LouDnl/USBSID-Pico/.github/wiki/Midi/Basics.md

# Midi basics
USBSID-Pico supports (Web)Midi over USB that acts as Midi device that can receive Midi commands.

See the [Midi Manual](https://github.com/LouDnl/USBSID-Pico/blob/master/doc/USBSID-Pico%20midi%20manual.adoc) on how you can use USBSID-Pico with Midi.
