LouDnl/USBSID-Pico/.github/wiki/Midi/Strudel.md

# Index
* [Strudel.cc](#strudelcc)
* [Notes](#notes)
* [Strudel examples](#strudel-examples)

# Strudel.cc
_Excerpt from Strudel website_
[Getting Started](https://strudel.cc/workshop/getting-started/)
With Strudel, you can expressively write dynamic music pieces.
It is an official port of the [Tidal Cycles](https://tidalcycles.org/) pattern language to JavaScript.
You don’t need to know JavaScript or Tidal Cycles to make music with Strudel. This interactive tutorial will guide you through the basics of Strudel.
The best place to actually make music with Strudel is the [Strudel REPL](https://strudel.cc)
## Strudel and USBSID-Pico
With it's WebMidi support you can use USBSID-Pico directly from your browser with [Strudel.cc](https://strudel.cc)

# Strudel Examples
See [.js examples](https://github.com/LouDnl/USBSID-Pico/tree/master/examples/midi/strudel/)
