LouDnl/USBSID-Pico/.github/wiki/Midi/TidalCycles.md

# Index
* [Tidal Cycles](#tidal-cycles)
* [SuperCollider Startup file (example)](#supercollider-startup-file-example)
* [Tidal examples](#tidal-examples)

# Tidal Cycles
_Excerpt from the Tidal Cycles website_
[Tidal Cycles](https://tidalcycles.org/) (or 'Tidal' for short) is a free/open source live coding environment for algorithmic patterns, written in Haskell. Tidal is using SuperCollider, another open-source software, for synthesis and I/O.
## Tidal Cycles and USBSID-Pico
With it's Midi over USB support you can use USBSID-Pico with [Tidal Cycles](https://tidalcycles.org/).  
This however does require you to follow the installation guide on the [documentation pages](https://tidalcycles.org/docs/).
* [Linux](https://tidalcycles.org/docs/getting-started/linux_install/)
* [MacOS](https://tidalcycles.org/docs/getting-started/macos_install/)
* [Windows](https://tidalcycles.org/docs/getting-started/windows_install/)

# SuperCollider Startup file (example)
See [startup.scd](https://github.com/LouDnl/USBSID-Pico/tree/master/examples/midi/superdirt-tidalcycles/startup.scd)

# Tidal examples
Below are my personal notes and scribbles, if they don't work then they don't work.
See [.tidal examples](https://github.com/LouDnl/USBSID-Pico/tree/master/examples/midi/superdirt-tidalcycles/)
