LouDnl/USBSID-Pico/doc/USBSID-Volume-daughterboard.pdf

# USBSID-Volume daughterboard

### Author: LouD - generated on 2026-07-08

# Table of Contents

# Disclaimer

I do this stuff in my free time for my enjoyment. Since I like to share my joy in creating this with everyone I try my best to provide a working PCB and Firmware. I am in no way an electronics engineer and can give no guarantees that this stuff does not break or damage your hardware, computer, phone, or whatever you try to hook it up to. Be sure to take great care when inserting any real MOS SID chips into the board. While everything has been tested with real chips, this is in no way a guarantee that nothing could go wrong. Use of this board and firmware at your own risk! I am in no way responsible for your damaged hardware. That being said, have fun!

# About

The volume daughterboard is intended as optional addon for USBSID-Pico.
With This board seated you can independently control the volume of the left and right audio channels.
The board is Plug and play compatible with v1.5+ boards.
Compatibility with v1.3 boards is possible with a small modification to provide voltage.

# Usage v1.5

Below is an example of the board seated.
Follow the instructions under Solder jumpers to configure the board for your pcb.


# Usage v1.3

Take great care when using the board with versions v1.3.
Below is an example of the board seated and as you can see the right most pins are unconnected. Follow the instructions under Solder jumpers and Voltage tap to configure the board for your pcb.


# Usage v1.0

Same as with v1.3, please take great care when using the board.
The v1.0 pcb only has 2 pins where the outer pin on each side is Ground. This requires you to make another mod to the board to provide ground to the board. Do this at your own risk, the board is not tested with v1.0 pcb’s.

# Solder jumpers

The board has 4 solder jumpers on the bottom that set the pin functions of 2 two outer most pins for each pinsocket.
These jumpers are marked with V-I-G or G-I-V, G for Ground, I for Input and V for Vdd.

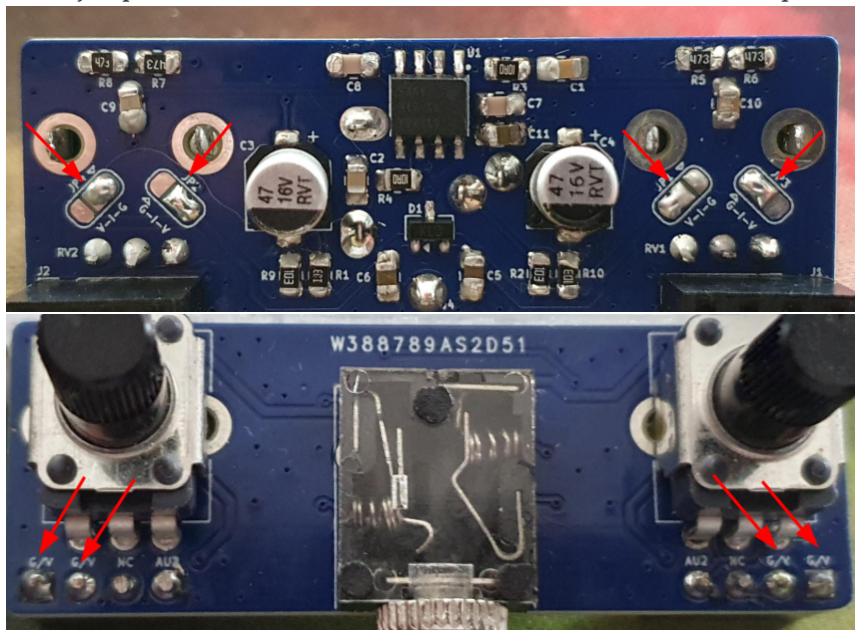
[picture p37: figure]

For v1.5 boards you can solder the jumpers exactly as the picture above, from left to right: V-I-G, G-I-V, V-I-G, G-I-V meaning Input+Ground, Input+VDD, VDD+Input, Ground+Input For v1.3 boards you can solder the jumpers as described below, from left to right:

V-I-G, G-I-V, V-I-G, G-I-V meaning VDD+Input, Ground+Input, Input+Ground, Input+VDD

The socket pins must match the order of the markings on the bottom of the USBSID-Pico PCB. v1.5:

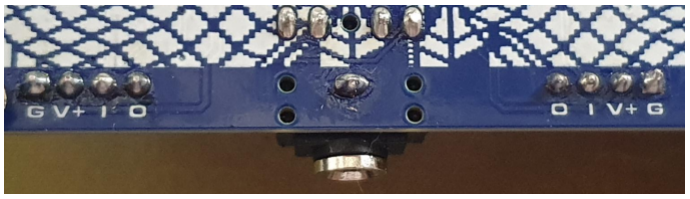
[picture p38: figure]

v1.3:

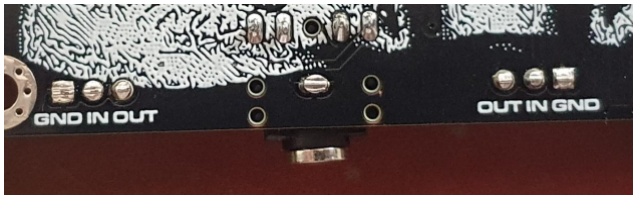
[picture p39: figure]

As you can see the v1.3 boards do not have a voltage pin, this requires you to make a voltage tap wire to any of the fixed points described under Voltage tap.

# Voltage tap

v1.3 pcbs have multiple points to where you can solder a wire to provide voltage to the volume board.
These tap points are described below the picture.

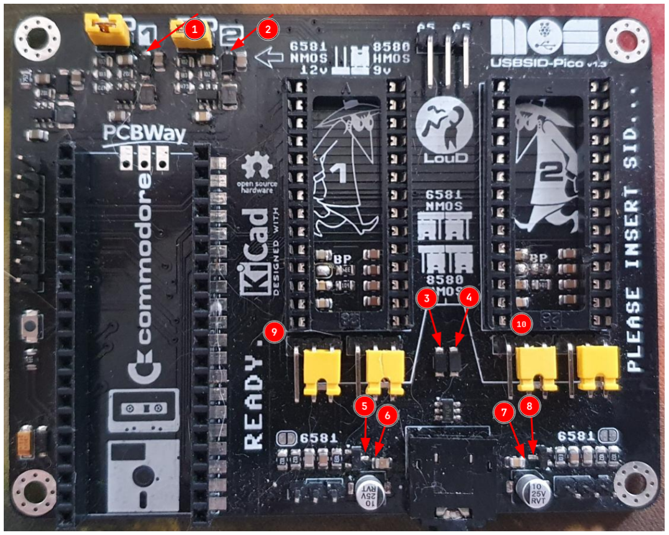
[picture p40: figure]

1. Diode output of SID1 voltage regulator 2. Diode output of SID2 voltage regulator 3. SID1 diode input voltage to audio switch 4. SID2 diode input voltage to audio switch 5. Voltage input to SID1 voltage follower 6. Voltage filter capacitor of SID1 voltage follower 7. Voltage input to SID2 voltage follower 8. Voltage filter capacitor of SID2 voltage follower 9. SID1 VDD in on the bottom of the PCB 10. SID2 VDD in on the bottom of the PCB

# License

# Software License ~ GNUv2

All code written by me in this repository is licensed under the terms of the GNU General Public License as published by the Free Software Foundation, version 2. Any code in this repository that is not written by me automatically falls under the licensing conditions by the authors of said code as mentioned in the source code header. For for more information about this license please read the LICENSE document in the root of the USBSID-Pico repository.

# Configtool Software License ~ EPLv2

# USBSID-Pico v1.5 PCB Hardware License ~ CC BY-NC-

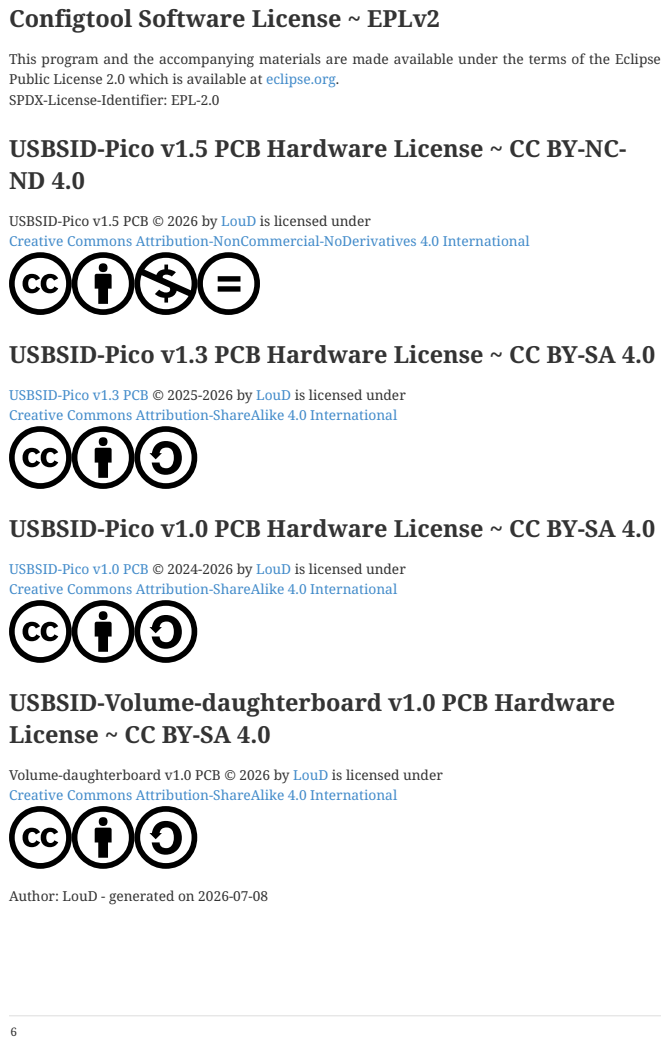
[picture p41: page 6]

This program and the accompanying materials are made available under the terms of the Eclipse
Public License 2.0 which is available at eclipse.org.
SPDX-License-Identifier: EPL-2.0

USBSID-Pico v1.5 PCB © 2026 by LouD (https://github.com/LouDnl) is licensed under
Creative Commons Attribution-NonCommercial-NoDerivatives 4.0 International (https://creativecommons.org/licenses/by-nc-nd/4.0/)

USBSID-Pico v1.3 PCB Hardware License ~ CC BY-SA 4.0

USBSID-Pico v1.3 PCB (https://github.com/LouDnl/USBSID-Pico/tree/master/hardware/USBSID-Pico-v1.3) © 2025-2026 by LouD (https://github.com/LouDnl) is licensed under
Creative Commons Attribution-ShareAlike 4.0 International (https://creativecommons.org/licenses/by-sa/4.0/)

USBSID-Pico v1.0 PCB Hardware License ~ CC BY-SA 4.0

USBSID-Pico v1.0 PCB (https://github.com/LouDnl/USBSID-Pico/tree/master/hardware/USBSID-Pico-v1.0) © 2024-2026 by LouD (https://github.com/LouDnl) is licensed under

USBSID-Volume-daughterboard v1.0 PCB Hardware
License ~ CC BY-SA 4.0

Volume-daughterboard v1.0 PCB © 2026 by LouD (https://github.com/LouDnl) is licensed under

Author: LouD - generated on 2026-07-08
