LouDnl/USBSID-Pico/SHOWCASE.md

# Showcase
Videos and/or audio links are subject to be changed or updated at any time.<br>
Visit my [Youtube channel](https://www.youtube.com/channel/UCOu1hPBTsEbG7ZFnk9-29KQ), [other socials](https://github.com/LouDnl) for more examples of the board in action.

### Audio recordings
- [Reed's Flamethrower](media/Reed-Flamethrower.mp3)
- [Fanta - Coma Light 13 (partial recording)](media/Fanta-ComaLight13(partial).mp3)
- [Fanta in Space (partial recording)](media/Fanta-InSpace(partial).mp3)
- [Jammer - Make Some Noise (partial recording)](media/Jammer-MakeSomeNoise(partial).mp3)
- [Mahoney - Musik Run Stop (partial recording)](media/Mahoney-MusikRunStop(partial).mp3)

### MOS8580 chip
| **Van Halen's Jump<br>in Stereo!** | **Flamethrower** | **Coma Light 13** |
|:-:|:-:|:-:|
| Dual MOS8580 (https://www.youtube.com/watch?v=lzvkWlDq2TM)<br><small><sub>by Nordischsound</sub></small> | MOS8580 (https://www.youtube.com/watch?v=Mfbj21ntQXA)<br><small><sub>by Reed</sub></small> | MOS8580 (https://www.youtube.com/watch?v=iXviof4ZtIg)<br><small><sub>by Oxyron</sub></small> |

| **Layers<br>Finnish Gold** | **Mojo<br>Bonzai & Pretzel Logic** | **Spy vs Spy II<br>The Island Caper** |
|:-:|:-:|:-:|
| MOS8580 (https://www.youtube.com/watch?v=UQVDTNV3mgs) | MOS8580 (https://www.youtube.com/watch?v=lXxlArB3VS4) | MOS8580 (https://www.youtube.com/watch?v=B4iYnZELbSc) |

| **Codeboys & Endians** | **No Limit** | **Multiverse 100%<br>with mirrored SID's!** |
|:-:|:-:|:-:|
| MOS8580 (https://www.youtube.com/watch?v=sSDsOih1Wbw)<br><small><sub>by Booze Design</sub></small> | MOS8580 (https://www.youtube.com/watch?v=hJit04tWUaM)<br><small><sub>Quantum tracker demo</sub></small> | Dual MOS8580 (https://www.youtube.com/watch?v=Rr-oq5jBeDg)<br><small><sub>by Nah-Kolor</sub></small> |

###  MOS6581 chip
| **“Raster Bar” (8-bit)** |
|:-:|
| MOS6581 (https://www.youtube.com/watch?v=nh0SxO1y6I0)<br><small><sub>by LukHash</sub></small> |

| **Spy vs Spy** | **Commando** | **Monty on the Run** |
|:-:|:-:|:-:|
| Dual MOS6581 (https://www.youtube.com/watch?v=Me79wiWPoXc) | Dual MOS6581 (https://www.youtube.com/watch?v=5YYzJu9KSuY) | Single MOS6581 (https://www.youtube.com/watch?v=PAHPY8jR4rA) <br><small><sub>by Rob Hubbard</sub></small> |

### Dual SIDKick-Pico with MOS8580 emulation
| **Still Rising**<br><small><sub>Single MOS8580</sub></small> | **The Ghost**<br><small><sub>Single MOS8580</sub></small> |
|:----:|:----:|
| Dual SIDKick-Pico (https://www.youtube.com/watch?v=svsxwElcWS8) <br>by Artline Designs,<br>Bloodsuckers,<br>Extend & Orange | Dual SIDKick-Pico (https://www.youtube.com/watch?v=joGVIwMuugU) <br>by FairLight<br>& Genesis Project |
| **Quad Core demo**<br><small><sub>Quad MOS8580</sub></small> | **Game of Thrones**<br><small><sub>Dual MOS8580</sub></small> |
| Dual SIDKick-Pico as 4x MOS8580 SID (https://www.youtube.com/watch?v=zWvMhORM-sg) <br>by Singular | Dual SIDKick-Pico (https://www.youtube.com/watch?v=lShZ3DHaJg8) <br>by Genesis Project |
