LouDnl/USBSID-Pico/cases/v1.3/spotUP-revisited/README.md

# Cartridge Case by spotUp revisited
- Updated to be v1.3 PCB compatible
- Optional reset button in top lid
  Printable reset pin included
- Optional open top lid
- Optional opening for RGB LED fun in top lid
- Optional openings for jumpers on the bottom in bottom lid
- Design is opensource  
  Change the case to your liking on [Tinkercad](https://www.tinkercad.com/things/9WenaLv3th5-usbsid-pico-v13-case)

# Examples
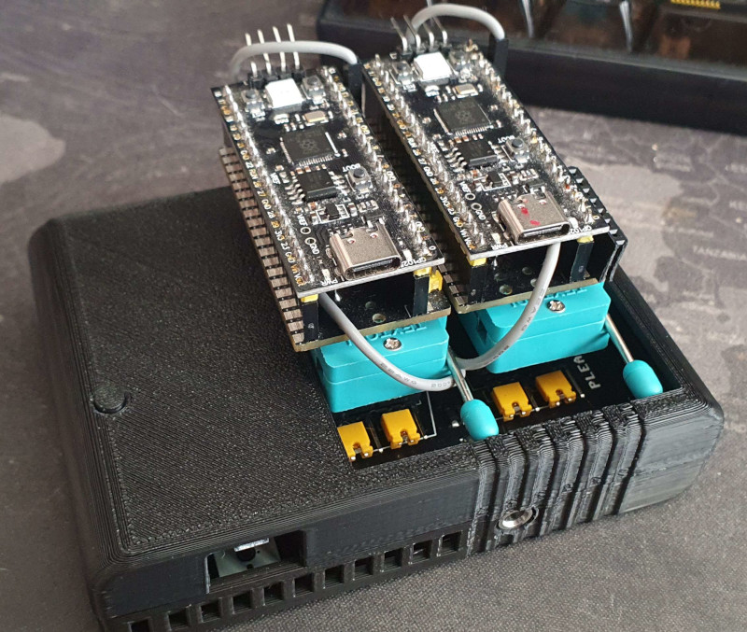
[picture p49: cases/v1.3/spotUP-revisited/v1.3-cartridgecase-top-open.jpg]
Cartridge Case Open Top
  

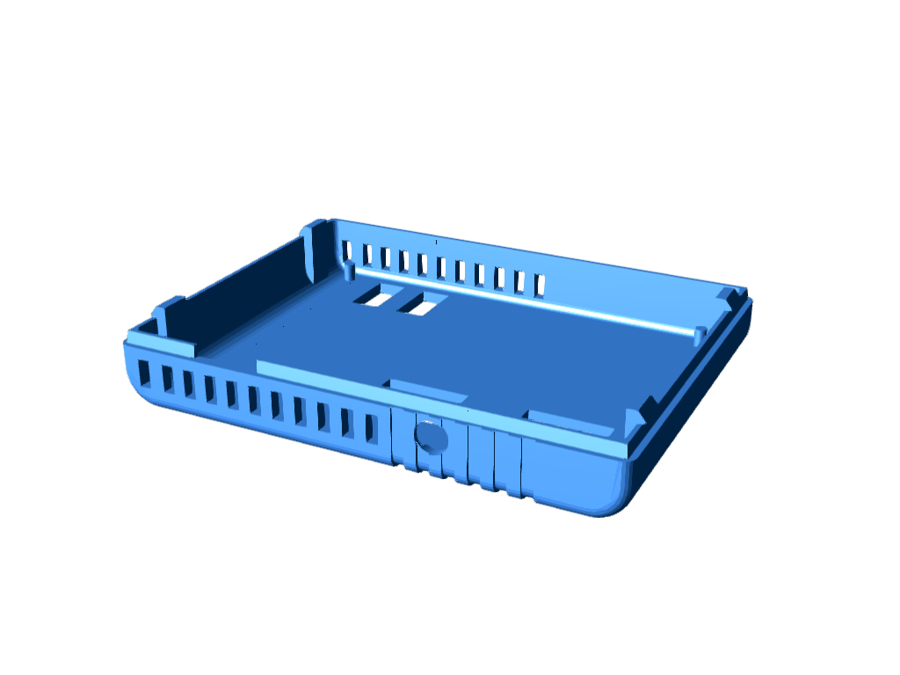
[picture p50: cases/v1.3/spotUP-revisited/USBSID-Pico v1.3 bottom case jumper openings.png]
bottom case

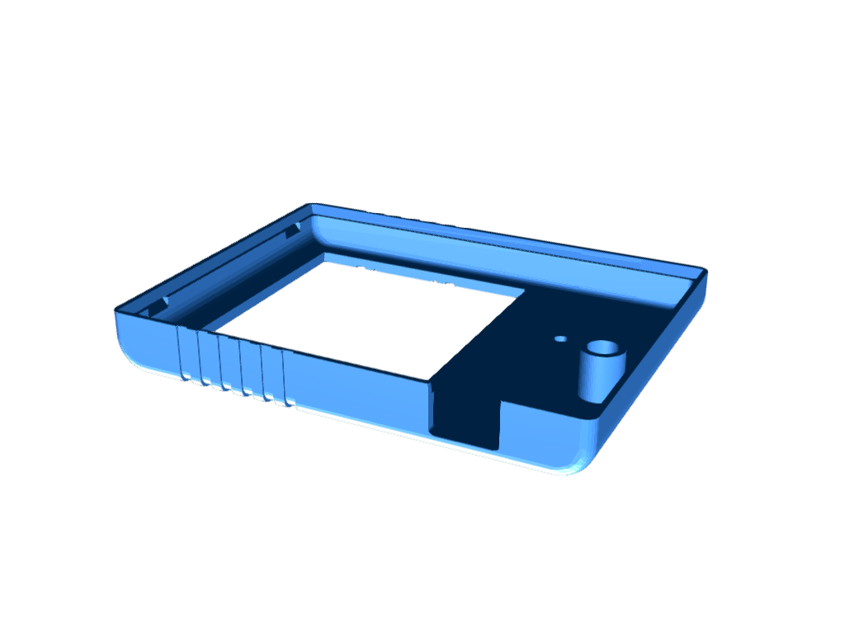
[picture p51: cases/v1.3/spotUP-revisited/USBSID-Pico v1.3 top case open with reset and rgb led opening.png]
top case


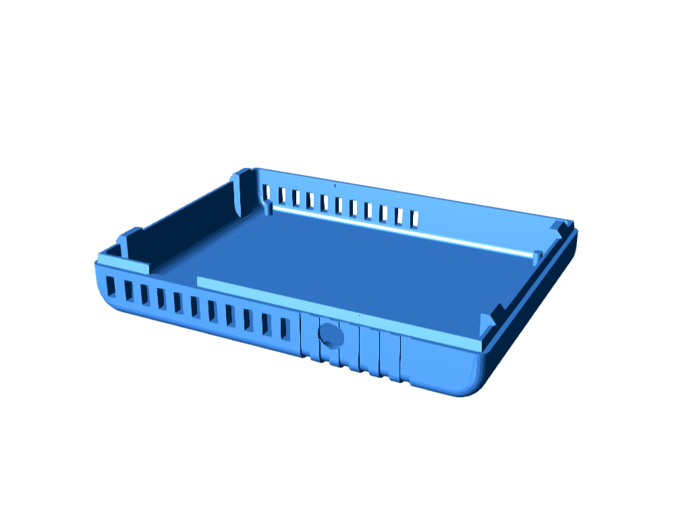
[picture p52: cases/v1.3/spotUP-revisited/USBSID-Pico v1.3 bottom case notched.png]
bottom case

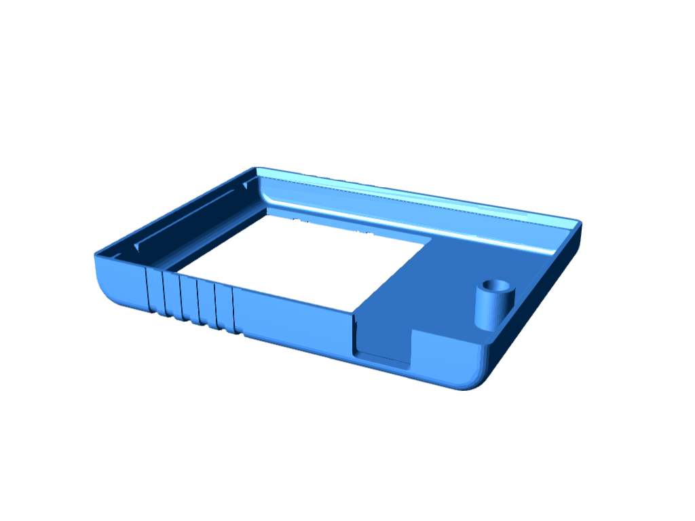
[picture p53: cases/v1.3/spotUP-revisited/USBSID-Pico v1.3 top case open with reset.png]
top case


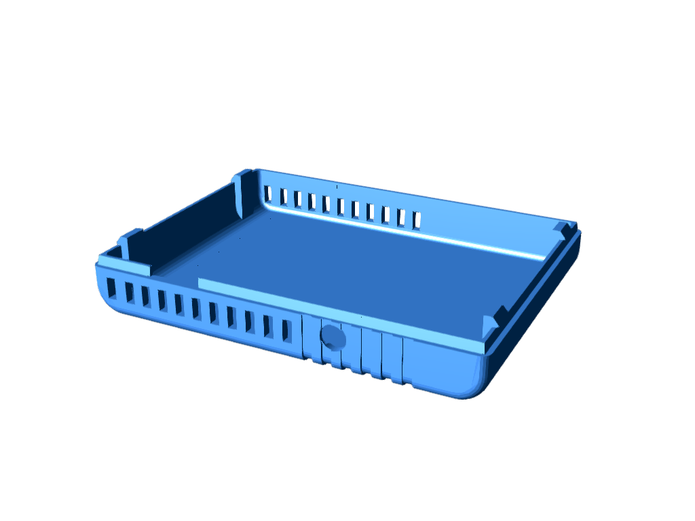
[picture p54: cases/v1.3/spotUP-revisited/USBSID-Pico v1.3 bottom case.png]
bottom case

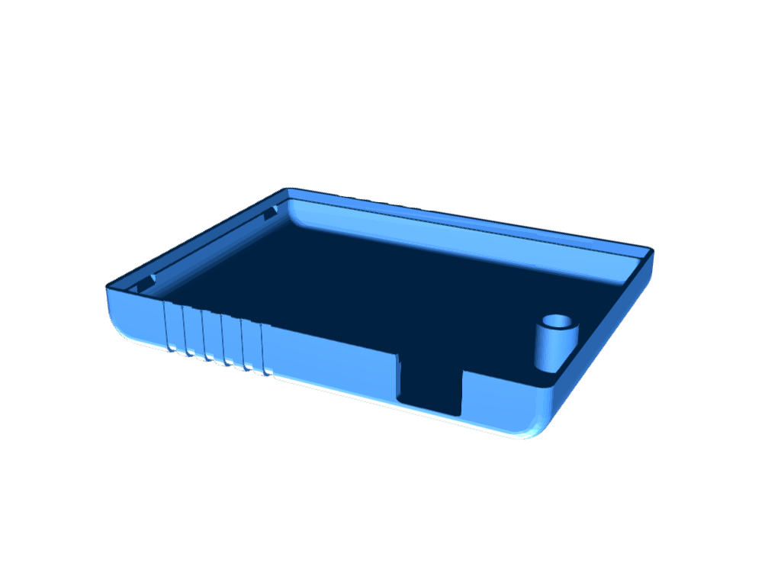
[picture p55: cases/v1.3/spotUP-revisited/USBSID-Pico v1.3 top case with reset.png]
top case
