LouDnl/USBSID-Pico/cases/v1.0/schorsch3000/Readme.md

# 3D-Printed 'boxy' case for the USBSID-pico

# Printing

For printing all you need are the two `.stl` files.

Just print the top and bottom part without support laying on the flat side.

If you want to print a multicolor logo, of a logo cutout, just split the case in parts in your slicer and color or remove the logo.

# Assembly
You'll need 4 M3 screws, 10-15mm in length.

You can tap the holes or just force the screw in.

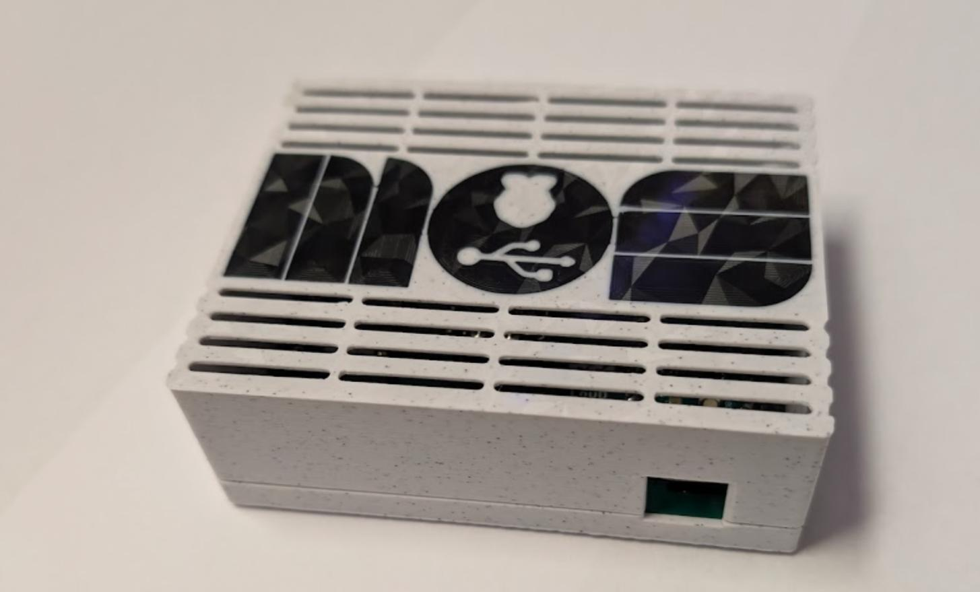
[picture p56: cases/v1.0/schorsch3000/top1.jpg]
top usb side


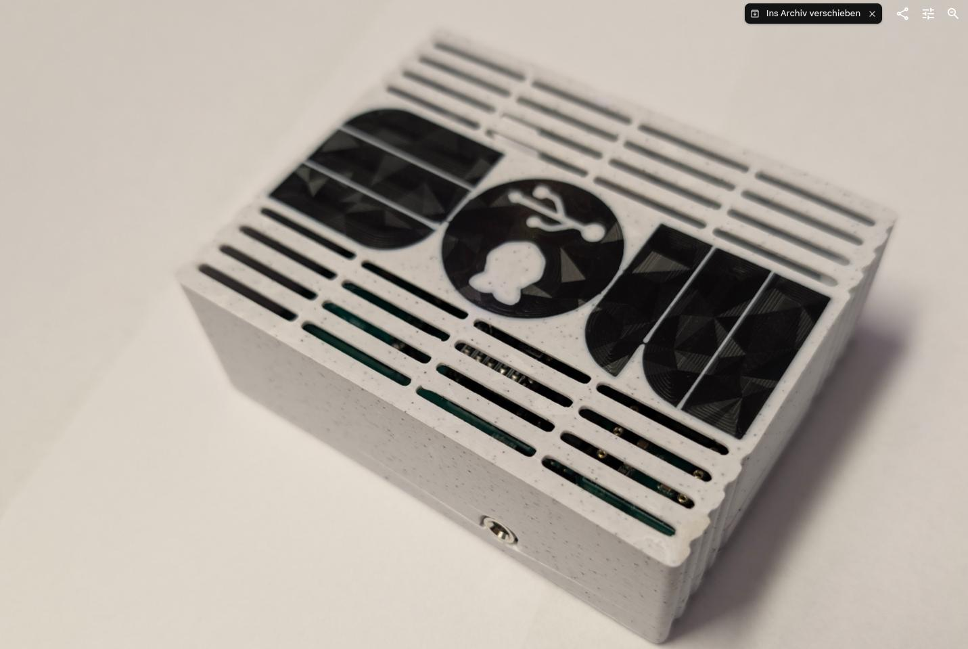
[picture p57: cases/v1.0/schorsch3000/top2.jpg]
top audio side

The Bulge at the Audioport is fixed by now.

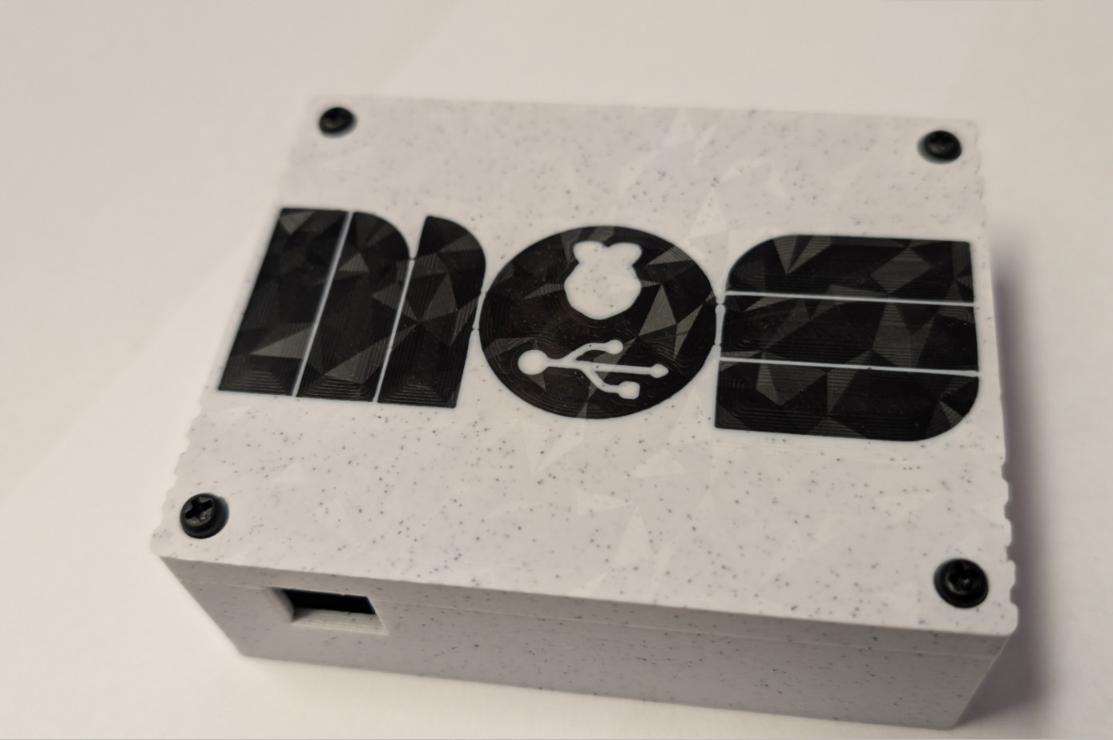
[picture p58: cases/v1.0/schorsch3000/bottom1.jpg]
bottom
