LouDnl/USBSID-Pico/doc/images/v1.5/usbsid-pico-v1.5b-6582-6581-original_1.jpg

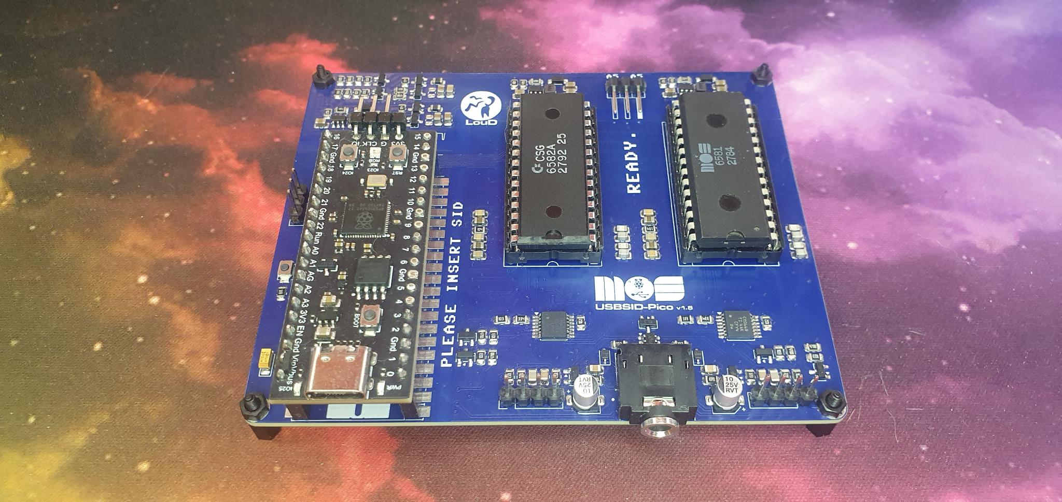
doc/images/v1.5/usbsid-pico-v1.5b-6582-6581-original_1.jpg
