LouDnl/USBSID-Pico/doc/images/v1.5/usbsid-pico-v1.5b-6582-6581-original_2.jpg

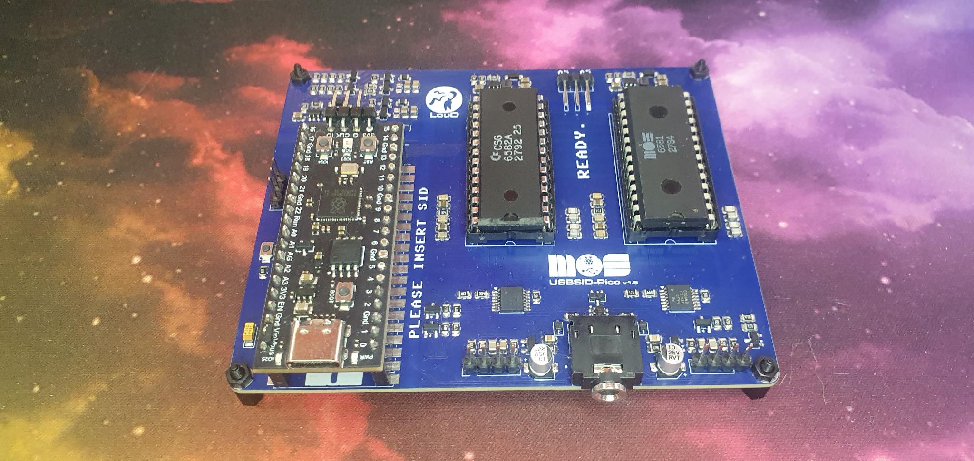
doc/images/v1.5/usbsid-pico-v1.5b-6582-6581-original_2.jpg
