LouDnl/USBSID-Pico/images/pcbv0.2.png

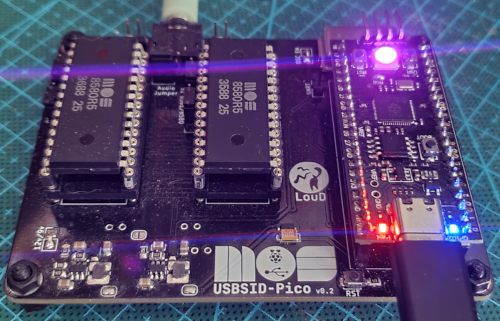
images/pcbv0.2.png
