LouDnl/USBSID-Pico/images/pcbv1.0.jpg

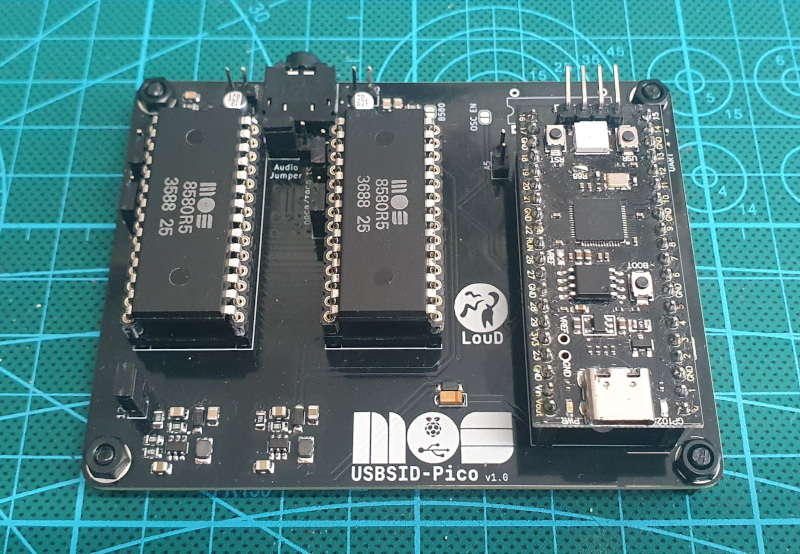
images/pcbv1.0.jpg
