LouDnl/USBSID-Pico/images/pcbv1.3-neon.png

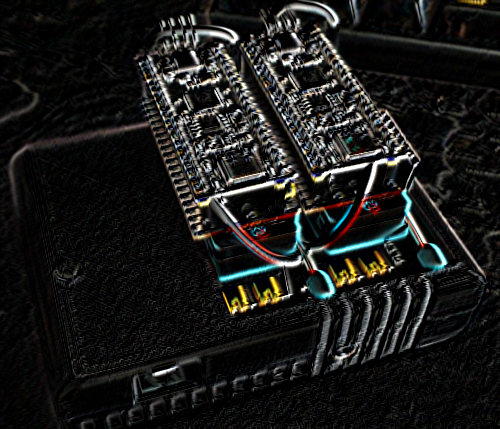
images/pcbv1.3-neon.png
