LouDnl/USBSID-Pico/images/pcbv1.3-pdsid.png

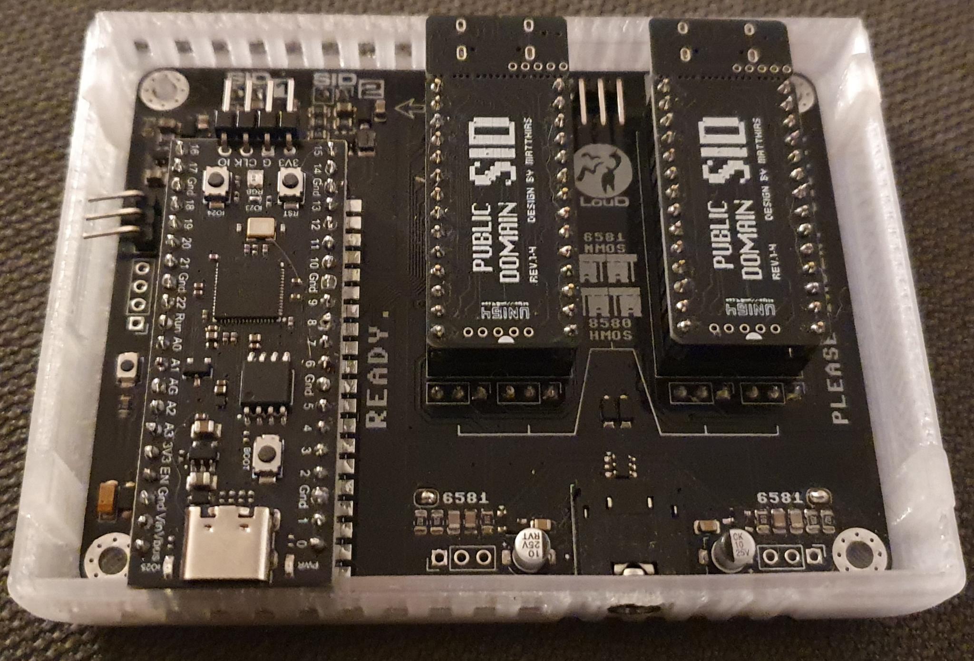
images/pcbv1.3-pdsid.png
