LouDnl/USBSID-Pico/images/pcbway.png

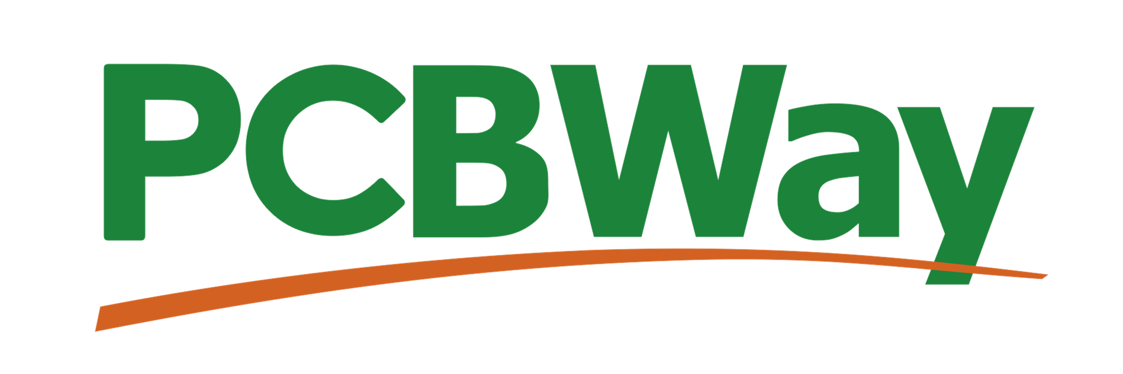
images/pcbway.png
