LouDnl/USBSID-Pico/hardware/v1.0-schematic.pdf

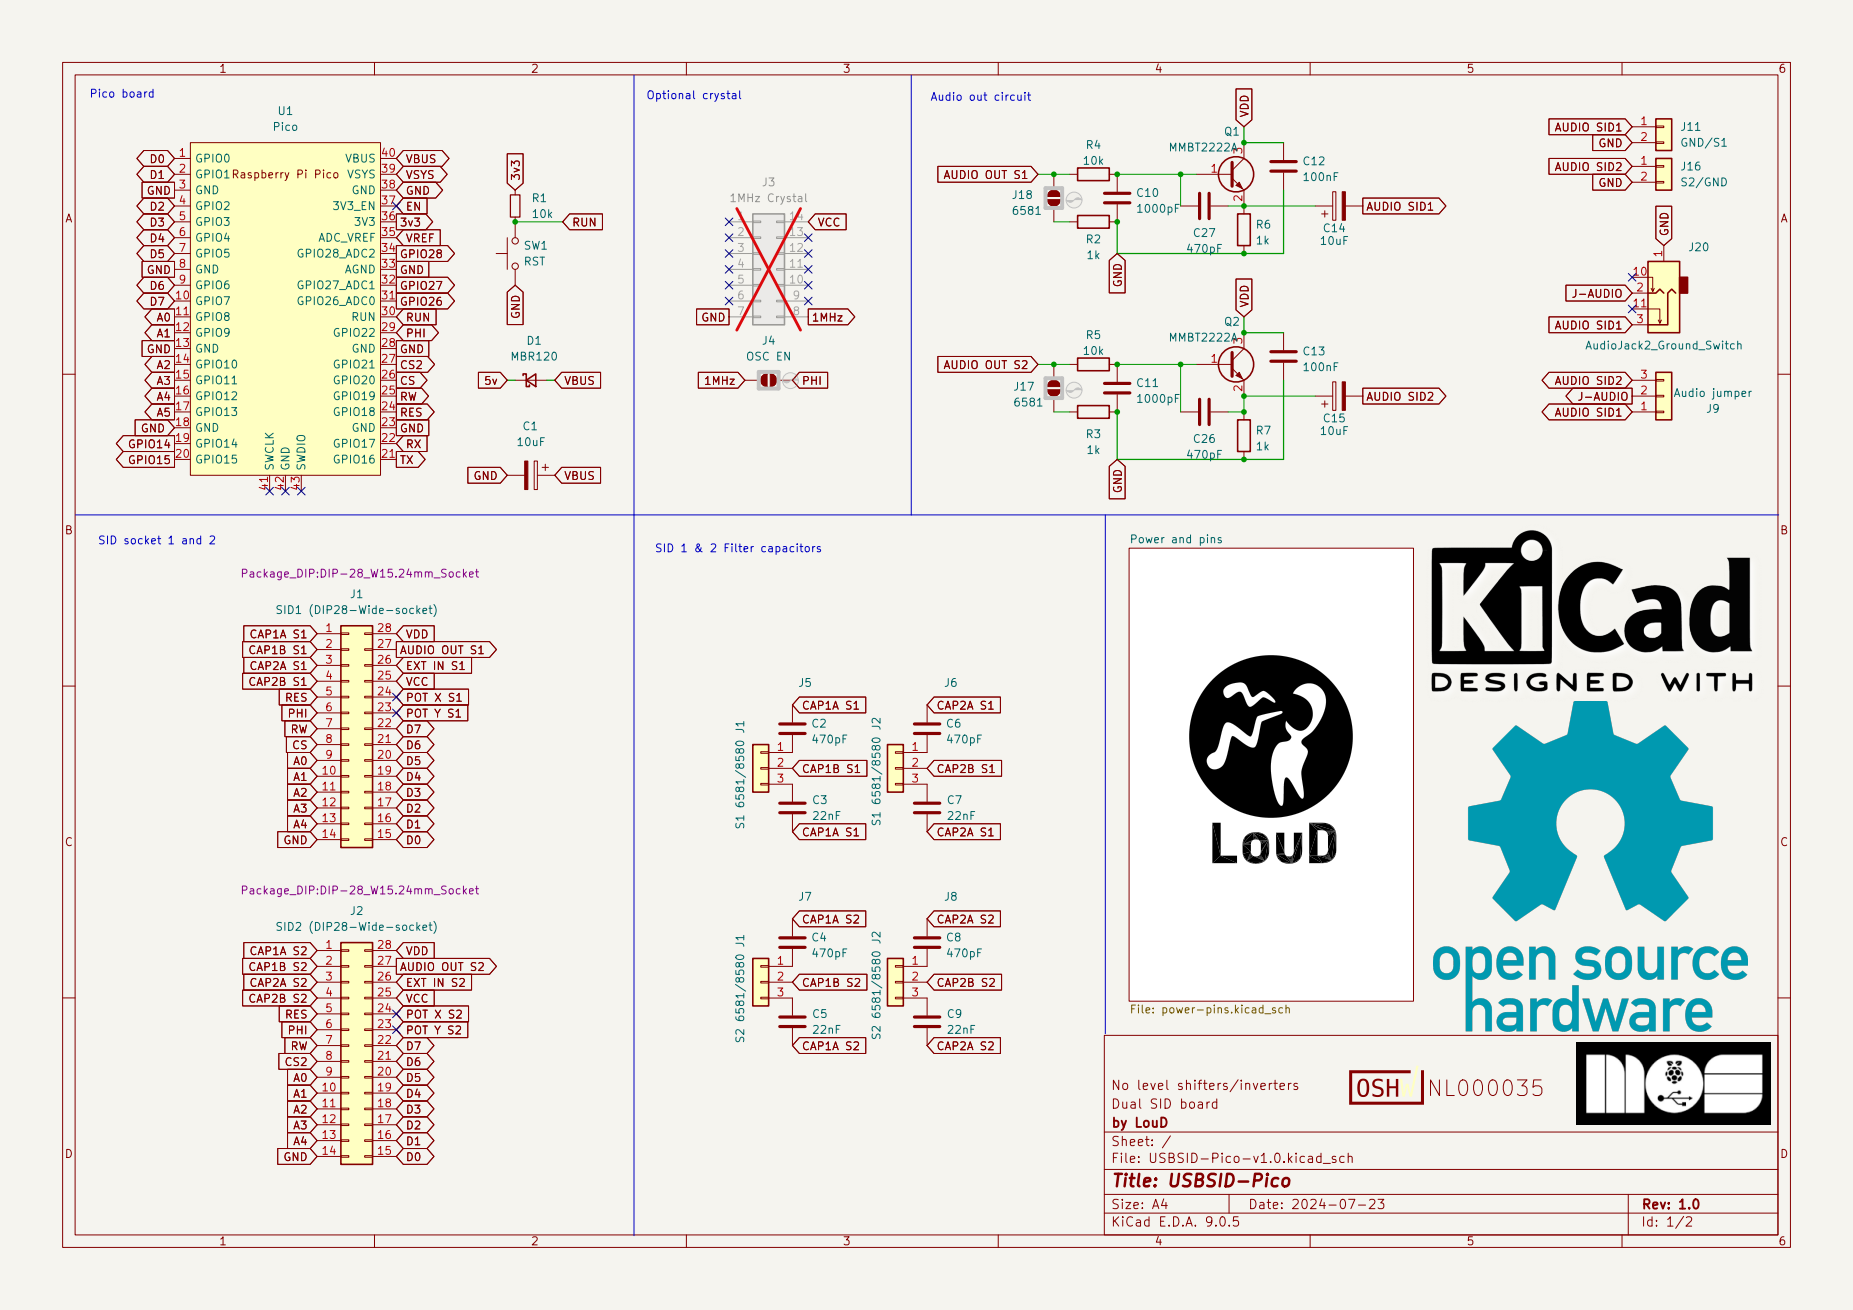
[picture p180: page 1]

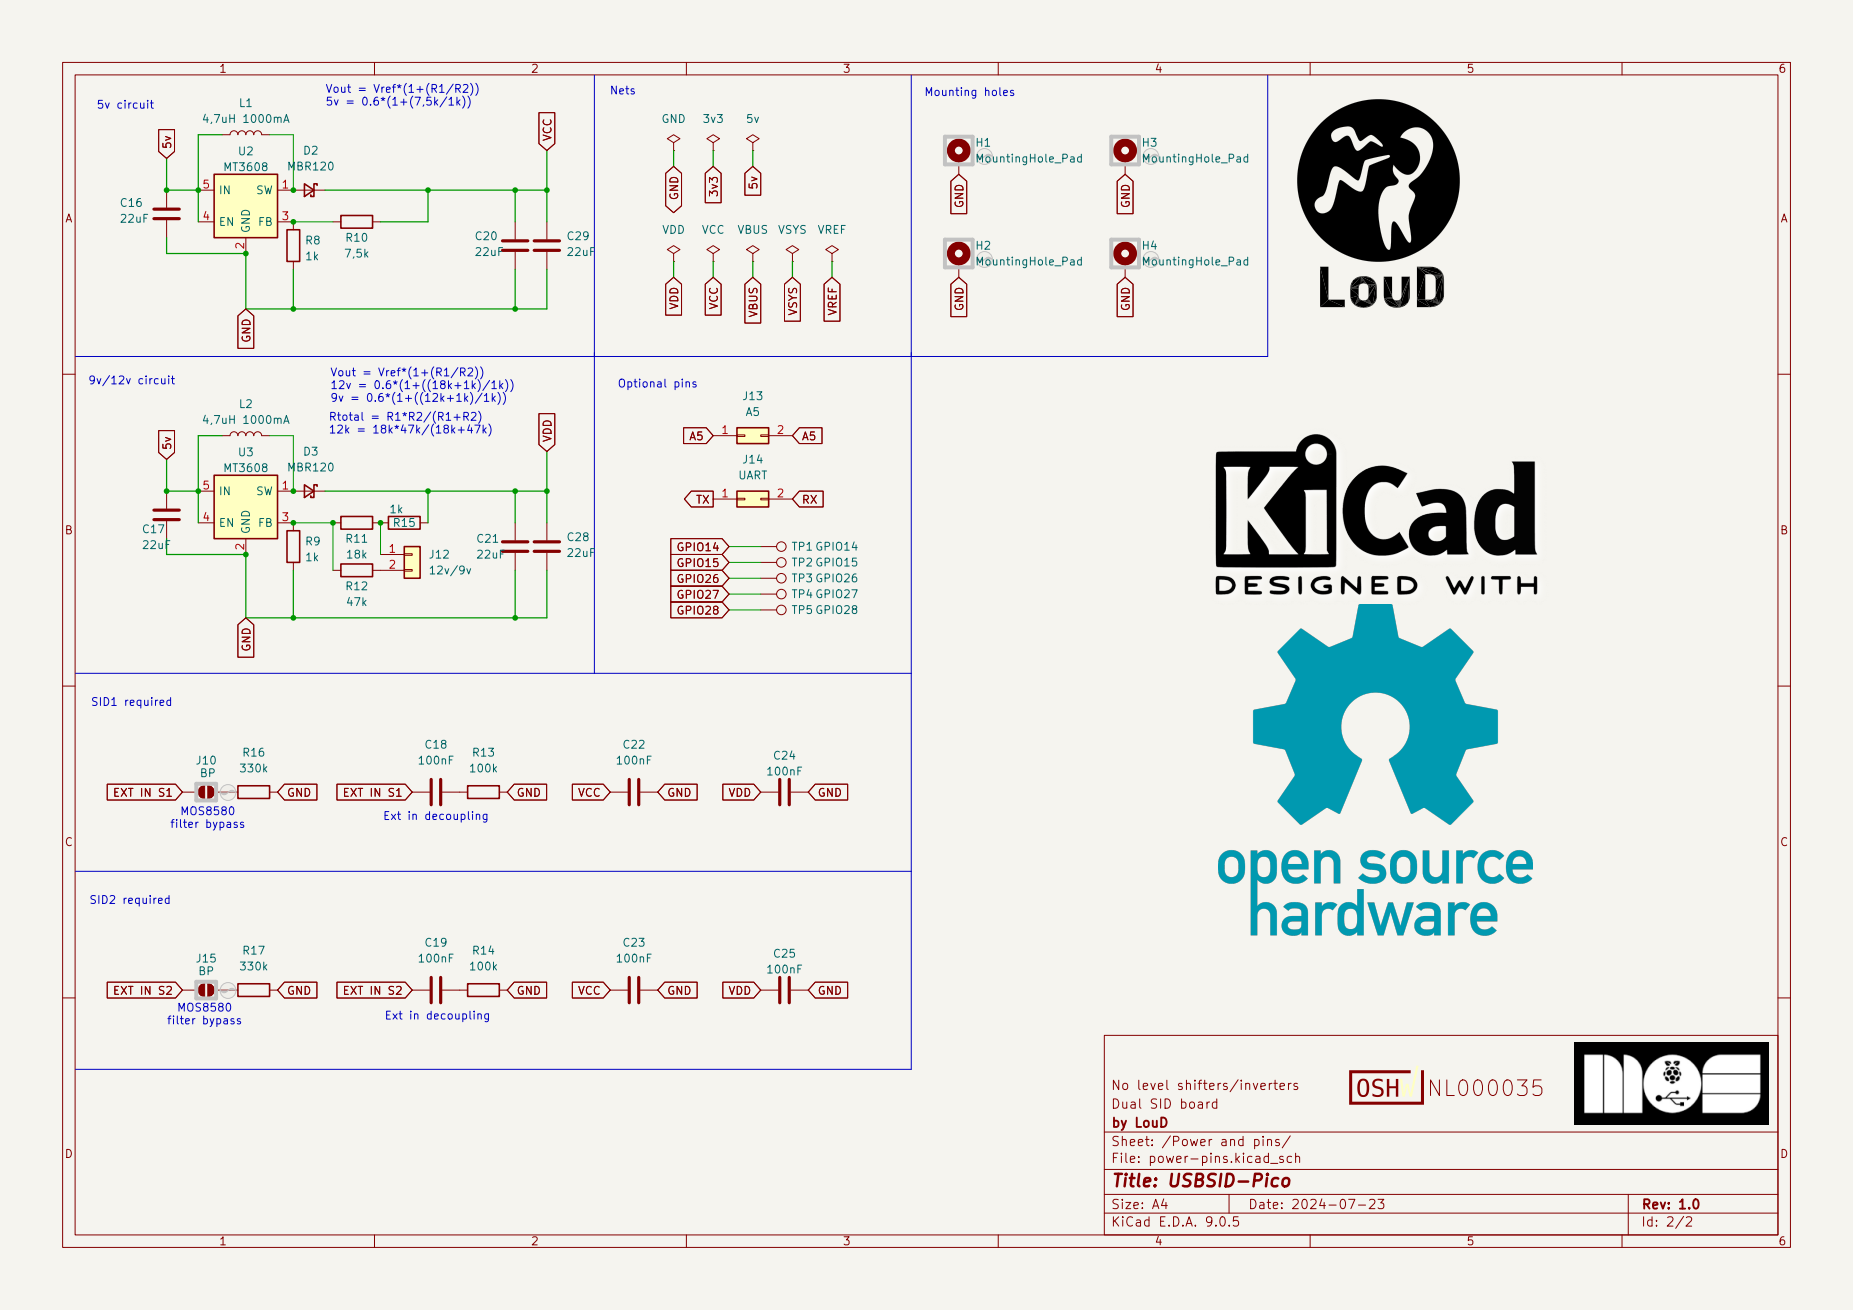
[picture p181: page 2]
