LouDnl/USBSID-Pico/src/sid_armsid.h

/*
 * USBSID-Pico is a RPi Pico/PicoW (RP2040) & Pico2/Pico2W (RP2350) based board
 * for interfacing one or two MOS SID chips and/or hardware SID emulators over
 * (WEB)USB with your computer, phone or ASID supporting player
 *
 * sid_armsid.h
 * This file is part of USBSID-Pico (https://github.com/LouDnl/USBSID-Pico)
 * File author: LouD
 *
 * Copyright (c) 2024-2026 LouD
 *
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
 */

#ifndef _USBSID_SID_ARMSID_H_
#define _USBSID_SID_ARMSID_H_
#pragma once

#ifdef __cplusplus
  extern "C" {
#endif


#define ARMSID_R1   0x1b /* 27 */
#define ARMSID_R2   0x1c /* 28 */

#define ARMSID_W1   0x1d /* 29 */
#define ARMSID_W2   0x1e /* 30 */
#define ARMSID_W3   0x1f /* 31 */

#define ARMSID_S    0x53 /* 'S' */
#define ARMSID_I    0x49 /* 'I' */
#define ARMSID_D    0x44 /* 'D' */
#define ARMSID_H    0x48 /* 'H' */
#define ARMSID_F    0x46 /* 'F' */
#define ARMSID_U    0x55 /* 'U' */
#define ARMSID_V    0x56 /* 'V' */

#define ARMSID_ID1  0x4e /* 'N' */
#define ARMSID_ID2  0x4f /* 'O' */

#define ARM2SID_ID1 0x02 /*  2 */
#define ARM2SID_ID2 0x4c /* 'L' */
#define ARM2SID_ID3 0x52 /* 'R' */

/* Reg    $1a $1b $1c $1d $1e $1f */
/* Socket 1 with ARMSID */
/* Read 1 $00 $4E $4F $53 $49 $44 ~ ARMSID identify */
/* Read 2 $FF $4E $4F $53 $69 $00 ~ Read all regs */
/* Read 3 $FF $4E $52 $53 $49 $49 ~ ARM2SID identify */
/* Read 4 $FF $45 $52 $53 $69 $00 ~ Read all regs */

/* Socket 2 with ARMSID */
/* Read 1 $00 $4E $4F $53 $49 $44 ~ ARMSID identify */
/* Read 2 $FF $4E $4F $53 $69 $00 ~ Read all regs */
/* Read 3 $FF $4E $52 $53 $49 $49 ~ ARM2SID identify */
/* Read 4 $FF $45 $52 $53 $49 $00 ~ Read all regs */

/* Reg    $1a $1b $1c $1d $1e $1f */
/* Socket 1 with ARM2SID */
/* Read 1 $00 $4E $4F $53 $49 $44 ~ ARMSID identify */
/* Read 2 $FF $4E $4F $53 $69 $00 ~ Read all regs */
/* Read 3 $FF $4E $4C $53 $49 $49 ~ ARM2SID identify */
/* Read 4 $FF $02 $4C $53 $69 $00 ~ Read all regs */

/* Socket 2 with ARM2SID */
/* Read 1 $00 $4E $4F $53 $49 $44 ~ ARMSID identify */
/* Read 2 $FF $4E $4F $53 $69 $00 ~ Read all regs */
/* Read 3 $FF $4E $4C $53 $49 $49 ~ ARM2SID identify */
/* Read 4 $FF $02 $4C $53 $69 $00 ~ Read all regs */

/* Reg    $1a $1b $1c $1d $1e $1f */
/* Socket 1 with ARMSID */
/* Read 1 $00 $4E $4F $53 $49 $44 ~ ARMSID identify */
/* Read 2 $00 $4E $52 $53 $49 $49 ~ ARM2SID identify */
/* Socket 2 with ARM2SID */
/* Read 1 $00 $4E $4F $53 $49 $44 ~ ARMSID identify */
/* Read 2 $00 $4E $4C $53 $49 $49 ~ ARM2SID identify */

#ifdef __cplusplus
  }
#endif

#endif /* _USBSID_SID_ARMSID_H_ */
