LouDnl/USBSID-Pico/src/dma.c

/*
 * USBSID-Pico is a RPi Pico/PicoW (RP2040) & Pico2/Pico2W (RP2350) based board
 * for interfacing one or two MOS SID chips and/or hardware SID emulators over
 * (WEB)USB with your computer, phone or ASID supporting player
 *
 * dma.c
 * This file is part of USBSID-Pico (https://github.com/LouDnl/USBSID-Pico)
 * File author: LouD
 *
 * Copyright (c) 2024-2026 LouD
 *
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
 */

#include <globals.h>
#include <logging.h>
#include <config.h>
#include <pio.h>
#include <bus.h>
#include <sid.h>


/* DMA */
int dma_tx_control = 0, dma_tx_data = 0, dma_rx_data = 0, dma_tx_delay = 0;
int dma_counter = 0;
#if PICO_RP2040
int dma_counter_chain = 0;
#endif
volatile uint32_t cycle_count_word;

/* Shiny things */
#if defined(PICO_DEFAULT_LED_PIN)
int dma_pwmled;
volatile int pwm_value = 0;
#if defined(USE_RGB)  /* No RGB LED on _w Pico's */
int dma_rgbled;
volatile uint32_t rgb_value = 0;
#endif
#endif


/**
 * @brief Claim and configure all bus and clock-counter DMA channels
 *
 * Claims dma_tx_control, dma_tx_data, dma_rx_data, dma_tx_delay and the
 * clock cycle counter channel(s), then configures each to feed/drain the
 * matching bus PIO state machine FIFO. The clock counter uses a single
 * endless-transfer channel on RP2350, and a two-channel ping-pong chain
 * on RP2040 (which lacks native endless transfer support), started
 * immediately so cycle_count_word updates continuously.
 *
 * @note do not manually assign DMA channel numbers, this causes a panic on
 *       the PicoW
 */
void setup_dmachannels(void)
{ /* NOTE: Do not manually assign DMA channels, this causes a Panic on the PicoW */
  usNFO("\n");
  usCFG("Init DMA Channels\n");

  /* NOTICE: DMA read address is disabled for now, it is causing confirmed desync on the rp2040 (rp2350 seems to works, but needs improving) */
  /* NOTICE: DMA chaining on rp2350 causes desync with cycled writes, probably due to RP2350-E8 */
  /* NOTE: Until I find a fix for the DMA chaining with the delay counter it's disabled */

  dma_tx_control = dma_claim_unused_channel(true);
  dma_tx_data = dma_claim_unused_channel(true);
  dma_rx_data = dma_claim_unused_channel(true);
  dma_tx_delay = dma_claim_unused_channel(true);
  dma_counter = dma_claim_unused_channel(true);
#if PICO_RP2040
  dma_counter_chain = dma_claim_unused_channel(true);
#endif

  { /* dma controlbus */
    dma_channel_config tx_config_control = dma_channel_get_default_config(dma_tx_control);
    channel_config_set_transfer_data_size(&tx_config_control, DMA_SIZE_8);
    channel_config_set_read_increment(&tx_config_control, false);
    channel_config_set_write_increment(&tx_config_control, false);
    channel_config_set_dreq(&tx_config_control, DREQ_PIO0_TX1);
    //#if PICO_PIO_VERSION == 0  /* rp2040 only for now, see notice above */
    //channel_config_set_chain_to(&tx_config_control, dma_tx_data); /* Chain to controlbus tx */
    //#endif
    dma_channel_configure(dma_tx_control, &tx_config_control, &bus_pio->txf[sm_control], NULL, 1, false);
  }

  { /* dma tx databus */
    dma_channel_config tx_config_data = dma_channel_get_default_config(dma_tx_data);
    channel_config_set_transfer_data_size(&tx_config_data, DMA_SIZE_32);
    channel_config_set_read_increment(&tx_config_data, false);
    channel_config_set_write_increment(&tx_config_data, false);
    channel_config_set_dreq(&tx_config_data, DREQ_PIO0_TX2);
    dma_channel_configure(dma_tx_data, &tx_config_data, &bus_pio->txf[sm_data], NULL, 1, false);
  }

  { /* dma rx databus */
    dma_channel_config rx_config_data = dma_channel_get_default_config(dma_rx_data);
    channel_config_set_transfer_data_size(&rx_config_data, DMA_SIZE_8);
    channel_config_set_read_increment(&rx_config_data, false);
    channel_config_set_write_increment(&rx_config_data, false);
    channel_config_set_dreq(&rx_config_data, DREQ_PIO0_RX1);
    dma_channel_configure(dma_rx_data, &rx_config_data, NULL, &bus_pio->rxf[sm_control], 1, false);
  }

  { /* dma delaytimerbus */
    dma_channel_config tx_config_delay = dma_channel_get_default_config(dma_tx_delay);
    channel_config_set_transfer_data_size(&tx_config_delay, DMA_SIZE_16);
    channel_config_set_read_increment(&tx_config_delay, false);
    channel_config_set_write_increment(&tx_config_delay, false);
    channel_config_set_dreq(&tx_config_delay, DREQ_PIO0_TX3);
    //#if PICO_PIO_VERSION == 0  /* rp2040 only for now, see notice above */
    //channel_config_set_chain_to(&tx_config_delay, dma_tx_control); /* Chain to controlbus tx */
    //#endif
    dma_channel_configure(dma_tx_delay, &tx_config_delay, &bus_pio->txf[sm_delay], NULL, 1, false);
  }
#if PICO_RP2350 /* RP2350 has native endless transfer support */
  { /* dma rx clock counter ~ should be an endless updating item */
    dma_channel_config clkcnt_config_data = dma_channel_get_default_config(dma_counter);
    channel_config_set_transfer_data_size(&clkcnt_config_data, DMA_SIZE_32);
    channel_config_set_read_increment(&clkcnt_config_data, false);
    channel_config_set_write_increment(&clkcnt_config_data, false);
    channel_config_set_dreq(&clkcnt_config_data, DREQ_PIO1_RX3);
    // channel_config_set_irq_ignore(&dma_counter, false);
    // dma_channel_configure(dma_counter, &clkcnt_config_data, &cycle_count_word, &bus_pio->rxf[sm_clkcnt], 1, false);
    cycle_count_word = 0;
    dma_channel_configure(
      dma_counter,
      &clkcnt_config_data,
      &cycle_count_word,
      &clkcnt_pio->rxf[sm_clkcnt],
      dma_encode_endless_transfer_count(), /* ENDLESS transfer count */
      true /* Start transfers immediately */
    );
  }
#else /* RP2040: ping-pong chain for continuous transfer */
  {
    cycle_count_word = 0;
    /* Channel A */
    dma_channel_config cfg_a = dma_channel_get_default_config(dma_counter);
    channel_config_set_transfer_data_size(&cfg_a, DMA_SIZE_32);
    channel_config_set_read_increment(&cfg_a, false);
    channel_config_set_write_increment(&cfg_a, false);
    channel_config_set_dreq(&cfg_a, DREQ_PIO1_RX3);
    channel_config_set_chain_to(&cfg_a, dma_counter_chain);
    dma_channel_configure(
      dma_counter,
      &cfg_a,
      &cycle_count_word,
      &clkcnt_pio->rxf[sm_clkcnt],
      1,
      false
    );

    /* Channel B - identical transfer, chains back to A */
    dma_channel_config cfg_b = dma_channel_get_default_config(dma_counter_chain);
    channel_config_set_transfer_data_size(&cfg_b, DMA_SIZE_32);
    channel_config_set_read_increment(&cfg_b, false);
    channel_config_set_write_increment(&cfg_b, false);
    channel_config_set_dreq(&cfg_b, DREQ_PIO1_RX3);
    channel_config_set_chain_to(&cfg_b, dma_counter);
    dma_channel_configure(
      dma_counter_chain,
      &cfg_b,
      &cycle_count_word,
      &clkcnt_pio->rxf[sm_clkcnt],
      1,
      false);

    /* Start channel A - it will chain to B, B chains back, forever */
    dma_channel_start(dma_counter_chain);
  }
#endif
#if PICO_RP2350
  usCFG("  DMA Channels claimed C:%d TX:%d RX:%d D:%d CNT:%d\n",
    dma_tx_control, dma_tx_data, dma_rx_data, dma_tx_delay, dma_counter);
#else
  usCFG("  DMA Channels claimed C:%d TX:%d RX:%d D:%d CNTA:%d CNTB:%d\n",
    dma_tx_control, dma_tx_data, dma_rx_data, dma_tx_delay, dma_counter, dma_counter_chain);
#endif

  return;
}

/**
 * @brief Claim and configure the VU LED DMA channels (PWM LED and RGB LED)
 *
 * Only runs when PICO_DEFAULT_LED_PIN is defined (no VU support on Pico W
 * boards). The RGB LED channel is additionally gated on USE_RGB.
 */
void setup_vu_dma(void)
{
  #if defined(PICO_DEFAULT_LED_PIN)  /* Cannot use VU on PicoW :( */
  { /* dma pwmled */
    dma_pwmled = dma_claim_unused_channel(true);
    dma_channel_config c_pwmled = dma_channel_get_default_config(dma_pwmled);
    channel_config_set_transfer_data_size(&c_pwmled, DMA_SIZE_32);
    channel_config_set_read_increment(&c_pwmled, false);
    channel_config_set_write_increment(&c_pwmled, false);
    channel_config_set_dreq(&c_pwmled, /* DREQ_PIO1_TX0 */DREQ_PIO1_TX1);
    dma_channel_configure(dma_pwmled, &c_pwmled, &led_pio->txf[sm_pwmled], &pwm_value, 1, true);
  }
  #if defined(USE_RGB)  /* No RGB LED on _w Pico's */
  { /* dma RGBled */
    dma_rgbled = dma_claim_unused_channel(true);
    dma_channel_config c_rgbled = dma_channel_get_default_config(dma_rgbled);
    channel_config_set_transfer_data_size(&c_rgbled, DMA_SIZE_32);
    channel_config_set_read_increment(&c_rgbled, false);
    channel_config_set_write_increment(&c_rgbled, false);
    channel_config_set_dreq(&c_rgbled, /* DREQ_PIO1_TX1 */DREQ_PIO1_TX2);
    dma_channel_configure(dma_rgbled, &c_rgbled, &led_pio->txf[sm_rgbled], &rgb_value, 1, true);
  }
  #endif
  #endif
}

/**
 * @brief Stop all in progress DMA transfers and
 *        clear bus PIO fifo's afterwards
 *
 */
void clear_dma_channels(void)
{ /* Abort the 4 bus DMA channels and flush the backing PIO FIFOs */
  /* Let any operation that is still travelling through the bus pipeline
     finish first, flushing the fifos underneath it leaves the delay
     statemachine stuck on `irq wait DATABUS` with both handshake flags
     set, which desyncs every write that follows */
  bool drained = bus_drain();

  uint32_t abort_mask = (1u << dma_tx_control) | (1u << dma_tx_data)
                      | (1u << dma_rx_data)    | (1u << dma_tx_delay)
#if PICO_RP2350
                      | (1u << dma_counter);
#else
                      | (1u << dma_counter)    | (1u << dma_counter_chain);
#endif
  /* RP2040-E13 / RP2350-E5: disable IRQ enables for these channels before
   * aborting so a pending completion cannot block the abort */
  uint32_t saved_inte0 = dma_hw->inte0 & abort_mask;
  hw_clear_bits(&dma_hw->inte0, abort_mask);
  /* Atomically abort all four channels */
  dma_hw->abort = abort_mask;
  while (dma_hw->abort & abort_mask) tight_loop_contents();
  /* Clear any spurious interrupt status raised during abort */
  dma_hw->ints0 = abort_mask;
  /* Restore interrupt enables */
  hw_set_bits(&dma_hw->inte0, saved_inte0);
  /* Flush PIO FIFOs so no stale data remains for the next transfer */
  clear_bus_fifos();
  /* The pipeline never ran empty, so the flush above may have truncated
     an operation halfway, put the bus statemachines back in step */
  if __us_unlikely(!drained) bus_resync();
  dma_hw->multi_channel_trigger =
#if PICO_RP2350
    (1u << dma_counter);
#else
    (1u << dma_counter)    | (1u << dma_counter_chain);
#endif
  return;
}

/**
 * @brief Abort the 4 bus DMA channels only, leaving the counter channel(s)
 *        and PIO/fifo state untouched. Used before a clock/PIO resync (see
 *        `apply_busclock_settings` and `apply_clockrate` in config.c), the
 *        fifo flush and statemachine resync there is done by the following
 *        `sync_pios(false)` call, not by this function.
 *
 *        The 4 bus DMA channels stay claimed, configured and enabled across
 *        the abort (`dma_channel_abort` never touches CTRL_EN); each is
 *        re-triggered on demand per bus operation with a freshly written
 *        buffer address (see bus.c), so there is nothing to re-arm
 *        afterwards. NOTE: never trigger these channels via
 *        `dma_hw->multi_channel_trigger` right after this call, it would
 *        replay whatever stale control/data word was still loaded when
 *        the abort below ran
 *
 */
void abort_dma_bustransfers(void)
{
  uint32_t abort_mask = (1u << dma_tx_control) | (1u << dma_tx_data)
                      | (1u << dma_rx_data)    | (1u << dma_tx_delay);
  /* RP2040-E13 / RP2350-E5: disable IRQ enables for these channels before
   * aborting so a pending completion cannot block the abort */
  uint32_t saved_inte0 = dma_hw->inte0 & abort_mask;
  hw_clear_bits(&dma_hw->inte0, abort_mask);
  /* Atomically abort all four channels */
  dma_hw->abort = abort_mask;
  while (dma_hw->abort & abort_mask) tight_loop_contents();
  /* Clear any spurious interrupt status raised during abort */
  dma_hw->ints0 = abort_mask;
  /* Restore interrupt enables */
  hw_set_bits(&dma_hw->inte0, saved_inte0);
  return;
}

/**
 * @brief Unclaim all bus, clock-counter and VU LED DMA channels
 *
 * Counterpart to setup_dmachannels/setup_vu_dma, used when restarting the
 * bus (see restart_bus in bus.c).
 */
void unclaim_dma_channels(void)
{
  /* disable delay timer dma */
  dma_channel_unclaim(dma_tx_delay);
  /* disable databus rx dma */
  dma_channel_unclaim(dma_rx_data);
  /* disable databus tx dma */
  dma_channel_unclaim(dma_tx_data);
  /* disable control bus dma */
  dma_channel_unclaim(dma_tx_control);

  /* disable counter dma */
  dma_channel_unclaim(dma_counter);
#if PICO_RP2040
  /* disable counter chain dma */
  dma_channel_unclaim(dma_counter_chain);
#endif

#if defined(PICO_DEFAULT_LED_PIN)
  /* disable pwmled dma */
  dma_channel_unclaim(dma_pwmled);
#if defined(USE_RGB)  /* No RGB LED on _w Pico's */
  /* disable rgbled dma */
  dma_channel_unclaim(dma_rgbled);
#endif
#endif
  return;
}
