LouDnl/USBSID-Pico/src/config_socket.c

/*
 * USBSID-Pico is a RPi Pico/PicoW (RP2040) & Pico2/Pico2W (RP2350) based board
 * for interfacing one or two MOS SID chips and/or hardware SID emulators over
 * (WEB)USB with your computer, phone or ASID supporting player
 *
 * config_socket.c
 * This file is part of USBSID-Pico (https://github.com/LouDnl/USBSID-Pico)
 * File author: LouD
 *
 * Copyright (c) 2024-2026 LouD
 *
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
 */

#include <globals.h>
#include <gpio.h>
#include <bus.h>
#include <dma.h>
#include <usbsid_constants.h>
#include <config.h>
#include <config_bus.h>
#include <midi.h>
#include <sid.h>
#include <sid_detection.h>
#include <logging.h>
#include <usbsid.h>


/* Pre declarations */
static SocketPreset detect_current_preset(void);
ConfigError validate_config(void);
Socket default_socket(int id);

/* Local volatile variable to stop any logging when detecting socket changes */
static volatile bool socket_logging = true;


/**
 * @brief Set the socket logging object
 *
 * @param boolean enabled
 */
void set_socketconfig_logging(bool enabled)
{
  socket_logging = enabled;
  return;
}

/**
 * @brief Helper function for retrieving the number of SID's configured
 *
 * @return uint8_t the number of sids configured
 */
uint8_t get_numsids(void)
{
  return cfg.numsids;
}

/**
 * @brief Returns the FMOpl SID number
 * @note Returns the configured SID id (not the socket slot index), since the
 * slot to id relation changes with disabled sockets and flipped/mixed presets
 *
 * @return int 1~4 the SID number, 0 when no FMOpl is configured
 */
int verify_fmopl_sidno(void)
{
  const SIDChip *sids[4] = {
    &usbsid_config.socketOne.sid1,
    &usbsid_config.socketOne.sid2,
    &usbsid_config.socketTwo.sid1,
    &usbsid_config.socketTwo.sid2,
  };

  for (int i = 0; i < 4; i++) {
    if (sids[i]->type == SID_FMOPL
      && sids[i]->addr != 0xFF
      && sids[i]->id < 4) {
      return sids[i]->id + 1;  /* Return 1-based SID number */
    }
  }

  return 0;  /* 0 = disabled */
}

/**
 * @brief Assign or clear the FMOpl SID type by SID number
 * @note The requested SID must have an address assigned, else the FMOpl type
 * would be reset to SID_NA by apply_sid_addresses() on the next apply
 *
 * @param int sidno 1~4 the SID number to set as FMOpl, 0 to clear
 * @return bool true when applied, false when the SID number is not addressable
 */
bool set_fmopl_sidno(int sidno)
{
  SIDChip *sids[4] = {
    &usbsid_config.socketOne.sid1,
    &usbsid_config.socketOne.sid2,
    &usbsid_config.socketTwo.sid1,
    &usbsid_config.socketTwo.sid2,
  };

  int slot = -1;
  if (sidno >= 1 && sidno <= 4) {
    for (int i = 0; i < 4; i++) {
      if (sids[i]->id == (sidno - 1) && sids[i]->addr != 0xFF) {
        slot = i;
        break;
      }
    }
    if (slot == -1) {
      usSOCK("FMOpl SID %d has no address assigned, not applied\n", sidno);
      return false;  /* Requested SID is not addressable, leave config untouched */
    }
  } else if (sidno != 0) {
    return false;  /* Out of range */
  }

  /* Clear any previously assigned FMOpl */
  for (int i = 0; i < 4; i++) {
    if (sids[i]->type == SID_FMOPL) {
      sids[i]->type = SID_UNKNOWN;
    }
  }
  if (slot != -1) {
    sids[slot]->type = SID_FMOPL;
  }

  return true;
}

/**
 * @brief Apply FMOpl configuration
 * @note changes both Config and the supplied RuntimeCFG
 *
 * @param RuntimeCFG *rt the runtime config to apply to
 */
void apply_fmopl_config(RuntimeCFG *rt)
{
  int fmopl_sid = verify_fmopl_sidno();
  usbsid_config.FMOpl.sidno = fmopl_sid;
  usbsid_config.FMOpl.enabled = (fmopl_sid != 0);
  if (rt != NULL) {
    rt->fmopl_sid = (uint8_t)fmopl_sid;
    rt->fmopl_enabled = usbsid_config.FMOpl.enabled;
  }
  return;
}

/**
 * @brief Convert SID address to default socket SID id
 *
 * @param uint8_t addr
 * @return uint8_t id
 */
uint8_t address_to_sid_id(uint8_t addr)
{
  switch (addr) {
    case 0x00: return 0;
    case 0x20: return 1;
    case 0x40: return 2;
    case 0x60: return 3;
    default:   return 0xFF;
  }
}

/**
 * @brief Convert socket SID id to SID address
 *
 * @param uint8_t id
 * @return uint8_t address
 */
uint8_t sid_id_to_address(uint8_t id)
{
  if (id < 4) {
    return sid_addresses[id];
  }
  return 0xFF;
}

/**
 * @brief Apply addresses to socket SID's
 *
 */
void apply_sid_addresses(void)
{
  /* Build index from socket flags */
  int idx = (
    (usbsid_config.socketOne.enabled ? 1 : 0) << 3)
    | ((usbsid_config.socketOne.dualsid ? 1 : 0) << 2)
    | ((usbsid_config.socketTwo.enabled ? 1 : 0) << 1)
    | ((usbsid_config.socketTwo.dualsid ? 1 : 0)
  );
  /* Override with extended table entries for flipped/mixed variants */
  if (idx == 10 && usbsid_config.flipped) {
    idx = 16;  /* Dual Stereo Flipped */
  } else if (idx == 15 && (usbsid_config.flipped || usbsid_config.mixed)) {
    idx = 16
      | (usbsid_config.flipped ? 1 : 0)  /* +1 -> 17: Quad Flipped */
      | (usbsid_config.mixed   ? 2 : 0); /* +2 -> 18: Quad Mixed, +3 -> 19: Both */
  }

  /* Lookup addresses from table */
  const uint8_t *addrs = address_table[idx];

  /* Apply to config */
  usbsid_config.socketOne.sid1.addr = addrs[0];
  usbsid_config.socketOne.sid2.addr = addrs[1];
  usbsid_config.socketTwo.sid1.addr = addrs[2];
  usbsid_config.socketTwo.sid2.addr = addrs[3];

  /* Compute IDs from addresses */
  usbsid_config.socketOne.sid1.id = address_to_sid_id(addrs[0]);
  usbsid_config.socketOne.sid2.id = address_to_sid_id(addrs[1]);
  usbsid_config.socketTwo.sid1.id = address_to_sid_id(addrs[2]);
  usbsid_config.socketTwo.sid2.id = address_to_sid_id(addrs[3]);

  /* Set disabled SID types to N/A */
  if (addrs[0] == 0xFF) usbsid_config.socketOne.sid1.type = SID_NA;
  if (addrs[1] == 0xFF) usbsid_config.socketOne.sid2.type = SID_NA;
  if (addrs[2] == 0xFF) usbsid_config.socketTwo.sid1.type = SID_NA;
  if (addrs[3] == 0xFF) usbsid_config.socketTwo.sid2.type = SID_NA;

  if (socket_logging) {
    usNFO("\n");
    usSOCK("SID addresses applied: S1.1=0x%02X S1.2=0x%02X S2.1=0x%02X S2.2=0x%02X (idx=%d)\n",
      addrs[0], addrs[1], addrs[2], addrs[3], idx);
  }

  return;
}

/**
 * @brief Apply Chip and SID detection results
 *
 * @param DetectionResult *det
 * @return ConfigError config validation
 */
ConfigError apply_detection_results(const DetectionResult *det)
{
  if (!det->success) {
    return det->error != CFG_OK ? det->error : CFG_ERR_DETECTION_FAILED;
  }

  /* Apply Socket 1 results */
  usbsid_config.socketOne.chiptype = det->socket[0].chiptype;
  usbsid_config.socketOne.dualsid = det->socket[0].supports_dual;
  usbsid_config.socketOne.enabled = det->socket[0].present;
  usbsid_config.socketOne.sid1.type = det->socket[0].sid1_type;
  usbsid_config.socketOne.sid2.type = det->socket[0].sid2_type;

  /* Apply Socket 2 results */
  usbsid_config.socketTwo.chiptype = det->socket[1].chiptype;
  usbsid_config.socketTwo.dualsid = det->socket[1].supports_dual;
  usbsid_config.socketTwo.enabled = det->socket[1].present;
  usbsid_config.socketTwo.sid1.type = det->socket[1].sid1_type;
  usbsid_config.socketTwo.sid2.type = det->socket[1].sid2_type;

  /* Ensure at least one socket is enabled */
  if (!usbsid_config.socketOne.enabled && !usbsid_config.socketTwo.enabled) {
    /* Fallback: enable only socket one and set both sockets to with unknown chip */
    usbsid_config.socketOne.enabled = true;
    usbsid_config.socketOne.chiptype = CHIP_UNKNOWN;
    usbsid_config.socketTwo.enabled = false;
    usbsid_config.socketTwo.chiptype = CHIP_UNKNOWN;
  }

  /* Recompute addresses based on new config */
  apply_sid_addresses();

  return validate_config();
}

/**
 * @brief Verifies detection results on socket change activity only
 *
 * @param DetectionResult *det
 * @return ConfigError
 */
ConfigError verify_socket_detection_results(const DetectionResult *det)
{
  usSOCK("Verifying socket detection results\n");
  if (!det->success) {
    return det->error != CFG_OK ? det->error : CFG_ERR_DETECTION_FAILED;
  }

  /* Verify Socket 1 results */
  bool s1check1 = (usbsid_config.socketOne.chiptype  != det->socket[0].chiptype);
  bool s1check2 = (usbsid_config.socketOne.dualsid   != det->socket[0].supports_dual);
  bool s1check3 = (usbsid_config.socketOne.enabled   != det->socket[0].present);
  /* Verify Socket 2 results */
  bool s2check1 = (usbsid_config.socketTwo.chiptype  != det->socket[1].chiptype);
  bool s2check2 = (usbsid_config.socketTwo.dualsid   != det->socket[1].supports_dual);
  bool s2check3 = (usbsid_config.socketTwo.enabled   != det->socket[1].present);
  if ((det->socket[0].chiptype == CHIP_REAL) && s1check1) {
    /* TODO: Do something here because voltage change!? */
  }
  if ((det->socket[1].chiptype == CHIP_REAL) && s2check1) {
    /* TODO: Do something here because voltage change!? */
  }

  /* Anything changed!? */
  if (s1check1 || s1check2 || s1check3
      || s2check1 || s2check2 || s2check3 ) {
    usSOCK("  SocketOne detected changes:\n");
    usSOCK("    Chip: %s was: %s detected: %s\n",
      changed_str(s1check1),
      chip_type_name(usbsid_config.socketOne.chiptype),
      chip_type_name(det->socket[0].chiptype));
    usSOCK("    Present: %s was: %s detected: %s\n",
      changed_str(s1check3),
      boolean_str(usbsid_config.socketOne.enabled),
      boolean_str(det->socket[0].present));
    usSOCK("    DualSID: %s was: %s detected: %s\n",
      changed_str(s1check2),
      boolean_str(usbsid_config.socketOne.dualsid),
      boolean_str(det->socket[0].supports_dual));
    usSOCK("  SocketTwo detected changes:\n");
    usSOCK("    Chip: %s was: %s detected: %s\n",
      changed_str(s1check1),
      chip_type_name(usbsid_config.socketTwo.chiptype),
      chip_type_name(det->socket[1].chiptype));
    usSOCK("    Present: %s was: %s detected: %s\n",
      changed_str(s2check3),
      boolean_str(usbsid_config.socketTwo.enabled),
      boolean_str(det->socket[1].present));
    usSOCK("    DualSID: %s was: %s detected: %s\n",
      changed_str(s2check2),
      boolean_str(usbsid_config.socketTwo.dualsid),
      boolean_str(det->socket[1].supports_dual));
    return CFG_ERR_CHANGE_DETECTED;
  }

  return CFG_OK;
}

/**
 * @brief Validate socket configuration for provided socket
 *
 * @param Socket *socket
 * @param int socket_num
 * @return ConfigError
 */
ConfigError validate_socket(const Socket *socket, int socket_num)
{
  if (socket == NULL) {
    return CFG_ERR_NULL_POINTER;
  }

  /* DualSID requires clone chiptype (real SIDs can't do dual) */
  if (socket->dualsid && socket->chiptype == CHIP_REAL) {
    usERR("Valdation error, Socket %d: DualSID on real chip\n", socket_num);
    return CFG_ERR_DUALSID_ON_REAL;
  }

  /* If socket enabled, primary SID must have valid address */
  if (socket->enabled && socket->sid1.addr == 0xFF) {
    usERR("Valdation error, Socket %d: Enabled but primary SID disabled\n", socket_num);
    return CFG_ERR_PRIMARY_SID_DISABLED;
  }

  return CFG_OK;
}

/**
 * @brief Validate the global configuration
 *
 * @return ConfigError
 */
ConfigError validate_config(void)
{
  /* At least one socket must be enabled */
  if (!usbsid_config.socketOne.enabled && !usbsid_config.socketTwo.enabled) {
    usERR("Valdation error, both sockets disabled!\n");
    return CFG_ERR_BOTH_SOCKETS_DISABLED;
  }

  /* Validate each socket independently
   * falls back to default configuration
   * if there is a configuration error */
SOCKONE:;
  err = validate_socket(&usbsid_config.socketOne, 1);
  if (err != CFG_OK) {
    usbsid_config.socketOne = default_socket(1);
    goto SOCKONE;
  }
SOCKTWO:;
  err = validate_socket(&usbsid_config.socketTwo, 2);
  if (err != CFG_OK) {
    usbsid_config.socketTwo = default_socket(2);
    goto SOCKTWO;
  }

  /* Check for address conflicts (unless mirrored) */
  if (!usbsid_config.mirrored) {
    uint8_t addrs[4] = {
      usbsid_config.socketOne.sid1.addr,
      usbsid_config.socketOne.sid2.addr,
      usbsid_config.socketTwo.sid1.addr,
      usbsid_config.socketTwo.sid2.addr,
    };

    for (int i = 0; i < 4; i++) {
      if (addrs[i] == 0xFF) continue;  /* Skip disabled slots */
      for (int j = i + 1; j < 4; j++) {
        if (addrs[j] == 0xFF) continue;
        if (addrs[i] == addrs[j]) {
          usERR("Address conflict: slot %d and %d both at 0x%02X\n",
            i, j, addrs[i]);
          return CFG_ERR_ADDRESS_CONFLICT;
        }
      }
    }
  }

  /* At least one SID must be usable (not N/A type) */
  bool has_usable_sid = false;

  if (usbsid_config.socketOne.enabled) {
    if (usbsid_config.socketOne.sid1.type != SID_NA && usbsid_config.socketOne.sid1.addr != 0xFF) {
      has_usable_sid = true;
    }
    if (usbsid_config.socketOne.dualsid &&
      usbsid_config.socketOne.sid2.type != SID_NA && usbsid_config.socketOne.sid2.addr != 0xFF) {
      has_usable_sid = true;
    }
  }
  if (usbsid_config.socketTwo.enabled) {
    if (usbsid_config.socketTwo.sid1.type != SID_NA && usbsid_config.socketTwo.sid1.addr != 0xFF) {
      has_usable_sid = true;
    }
    if (usbsid_config.socketTwo.dualsid &&
      usbsid_config.socketTwo.sid2.type != SID_NA && usbsid_config.socketTwo.sid2.addr != 0xFF) {
      has_usable_sid = true;
    }
  }

  /* Allow unknown SID types (detection might not have run yet) */
  if (!has_usable_sid) {
    /* Check if any SID has unknown type (acceptable pre-detection) */
    bool has_unknown = (
      usbsid_config.socketOne.enabled && usbsid_config.socketOne.sid1.type == SID_UNKNOWN)
      || (usbsid_config.socketTwo.enabled && usbsid_config.socketTwo.sid1.type == SID_UNKNOWN
    );
    if (!has_unknown) {
      usERR("No usable SID found!\n");
      return CFG_ERR_NO_VALID_SID;
    }
  }

  /* Set current matching preset in config */
  usbsid_config.last_preset = detect_current_preset();

  return CFG_OK;
}

/**
 * @brief Flip socket addresses and id's at runtime
 *
 */
void flip_sockets(void)
{
  /* Swap IDs between sockets */
  uint8_t tmp_id;
  uint8_t tmp_addr;

  /* Swap SID1 */
  tmp_id = usbsid_config.socketOne.sid1.id;
  tmp_addr = usbsid_config.socketOne.sid1.addr;
  usbsid_config.socketOne.sid1.id = usbsid_config.socketTwo.sid1.id;
  usbsid_config.socketOne.sid1.addr = usbsid_config.socketTwo.sid1.addr;
  usbsid_config.socketTwo.sid1.id = tmp_id;
  usbsid_config.socketTwo.sid1.addr = tmp_addr;

  /* Swap SID2 */
  tmp_id = usbsid_config.socketOne.sid2.id;
  tmp_addr = usbsid_config.socketOne.sid2.addr;
  usbsid_config.socketOne.sid2.id = usbsid_config.socketTwo.sid2.id;
  usbsid_config.socketOne.sid2.addr = usbsid_config.socketTwo.sid2.addr;
  usbsid_config.socketTwo.sid2.id = tmp_id;
  usbsid_config.socketTwo.sid2.addr = tmp_addr;

  apply_runtime_config(&usbsid_config, &cfg);

  /* Reset SID registers after fiddling with the socket configuration */
  reset_sid_registers();

  return;
}

/**
 * @brief Helper funtion to apply requested socket preset
 *
 * @param SocketPreset preset
 */
static void apply_socket_preset(SocketPreset preset)
{
  /* Applying a preset makes sure that the clockspeed
     is set to PAL if still at the default 1MHz */
  if (usbsid_config.clock_rate == CLOCK_DEFAULT) {
    usbsid_config.clock_rate   = CLOCK_PAL;
    usbsid_config.refresh_rate = HZ_50;
    usbsid_config.raster_rate  = R_PAL;
  }

  const PresetDef *p = &socket_presets[preset];

  /* Apply preset flags */
  usbsid_config.socketOne.enabled = p->s1_enabled;
  usbsid_config.socketOne.dualsid = p->s1_dual;
  usbsid_config.socketTwo.enabled = p->s2_enabled;
  usbsid_config.socketTwo.dualsid = p->s2_dual;
  usbsid_config.mirrored = p->mirrored;
  usbsid_config.flipped = p->flipped;
  usbsid_config.mixed = p->mixed;

  /* Validate dualsid/chiptype compatibility */
  if (p->s1_dual && usbsid_config.socketOne.chiptype == CHIP_REAL) {
    /* Upgrade to unknown clone if needed for dualsid */
    usbsid_config.socketOne.chiptype = CHIP_UNKNOWN;
  }
  if (p->s2_dual && usbsid_config.socketTwo.chiptype == CHIP_REAL) {
    /* Upgrade to unknown clone if needed for dualsid */
    usbsid_config.socketTwo.chiptype = CHIP_UNKNOWN;
  }

  /* Compute addresses for this preset */
  apply_sid_addresses();

  return;
}

/**
 * @brief Helper function to detect an active preset
 *
 * @return SocketPreset
 */
static SocketPreset detect_current_preset(void)
{
  for (int i = 0; i < PRESET_COUNT; i++) {
    const PresetDef *p = &socket_presets[i];
    if (usbsid_config.socketOne.enabled == p->s1_enabled &&
      usbsid_config.socketOne.dualsid == p->s1_dual &&
      usbsid_config.socketTwo.enabled == p->s2_enabled &&
      usbsid_config.socketTwo.dualsid == p->s2_dual &&
      usbsid_config.mirrored == p->mirrored &&
      usbsid_config.flipped == p->flipped &&
      usbsid_config.mixed == p->mixed) {
      return (SocketPreset)i;
    }
  }

  return PRESET_COUNT;  /* No match */
}

/**
 * @brief Apply requested preset only if not already active
 *
 * @param SocketPreset preset
 * @return ConfigError
 */
static ConfigError apply_preset(SocketPreset preset)
{
  if (preset < 0 || preset >= PRESET_COUNT) {
    return CFG_ERR_INVALID_PRESET;
  }

  SocketPreset pre = detect_current_preset();
  if (pre == preset) {
    return CFG_ERR_EQUAL_PRESET;
  }

  /* Run autodetection before applying preset if enabled,
     this will ensure supporting chips and sids, etc */
  if (usbsid_config.preset_auto_detect) {
    sid_auto_detect_silent();
  }

  apply_socket_preset(preset);

  /* Validate the result */
  err = apply_new_presetconfig();
  set_socketconfig_logging(true); /* Enable logging */
  if (err != CFG_OK) {
    usERR("Preset '%s' validation failed: %s\n", preset_name(preset), config_error_str(err));
  } else {
    usbsid_config.last_preset = preset;
  }

  return err;
}

/**
 * @brief Wraps around apply_preset for non boot presets
 *        called from config.c:handle_config_request() only!!
 *
 * @param SocketPreset preset
 */
void apply_preset_wrapper(SocketPreset preset)
{
  /* Completely disable logging */
  set_socketconfig_logging(false);
  set_detection_logging(false);

  /* Backup global */
  uint32_t irq = save_and_disable_interrupts();
  Config backup_cfg;
  memcpy(&backup_cfg, &usbsid_config, sizeof(Config));
  restore_interrupts(irq);

  /* Now apply the preset */
  err = apply_preset(preset);
  if (err != CFG_OK) {
    memcpy(&usbsid_config, &backup_cfg, sizeof(Config)); /* Reset the config back */
    usWRN("Did not apply requested preset: %s\n", config_error_str(err));
    return;
  }

  /* Save and load the config */
  save_load_config();

  /* Re-enable logging */
  set_socketconfig_logging(true);
  set_detection_logging(true);

  usNFO("\n");
  usSOCK("Preset applied: %s\n", preset_name(preset));
  return;
}

/**
 * @brief Returns default Socket configuration
 *
 * @param int id, the socket id 1 or 2
 */
Socket default_socket(int id)
{
  const SIDChip s1s1 = {
    .id = 0,
    .addr = 0x00,
    .type = SID_UNKNOWN,
  };
  const SIDChip s2s1 = {
    .id = 1,
    .addr = 0x20,
    .type = SID_UNKNOWN,
  };
  const SIDChip sNs2 = {
    .id = 0xff,
    .addr = 0xff,
    .type = SID_NA,
  };
  Socket socket_conf = {
    .enabled = true,
    .dualsid = false,
    .chiptype = CHIP_REAL,
    .sid1 = (id == 1 ? s1s1 : s2s1),
    .sid2 = sNs2,
  };
  return socket_conf;
}

/**
 * @brief Applies the default socket
 *        and runtime configuration if required
 */
void socket_config_fallback(void)
{
  if (socket_logging) usSOCK("Applying socket fallback configuration\n");
  /* Socket One */
  usbsid_config.socketOne = default_socket(1);
  /* Socket Two */
  usbsid_config.socketTwo = default_socket(2);
  /* General */
  usbsid_config.mirrored = false;
  usbsid_config.flipped = false;
  usbsid_config.mixed = false;

  RuntimeCFG new_cfg;
  apply_runtime_config(&usbsid_config, &new_cfg); /* Quietly apply the bus config */
  uint32_t irq = save_and_disable_interrupts();
  memcpy(&cfg, &new_cfg, sizeof(RuntimeCFG));
  restore_interrupts(irq);

  return;
}

/**
 * @brief Autodetection for sock chip change
 * @note Any change _will_ lock USBSID untill verification
 *
 * @return ConfigError CFG_OK when no change detected, otherwise the detected change/error code
 */
ConfigError detect_socket_change(void)
{
  /* Disable logging */
  set_socketconfig_logging(false);
  set_detection_logging(false);
  set_busconfig_logging(false);

#if PCB_VERSION_INT >= 15
  /* Set base voltages, only does anything if PCB version is >= v1.5 */
  set_base_voltages(500); /* Logically also resets the SID */
#endif

  /* Run detection */
  DetectionResult det = detect_all();

  /* Verify results */
  ConfigError change_detected = verify_socket_detection_results(&det);

  err = apply_detection_results(&det);
  if (err != CFG_OK) {
    usERR("Error applying detection results: %s\n", config_error_str(err));
  }

  /* Re-enable logging */
  set_socketconfig_logging(true);
  set_busconfig_logging(true);
  set_detection_logging(true);

  /* Detection mixes fire and forget writes with cpu side irq handling,
     which can leave the bus pipeline one word out of step. Nothing else
     in the boot path re-initialises the bus statemachines after this
     point, so realign them here or every cycled write from now on gets
     paired with the wrong delay value */
  bus_drain();   /* Let the last register writes land */
  bus_resync();  /* Then put the pipeline back in a known state */

  if (change_detected != CFG_OK) {
    usWRN("SID Protection: %s\n", config_error_str(change_detected));
#if PCB_VERSION_INT >= 15
    voltage_state_off(); /* Turn off regulators if change detected */
#endif
    return change_detected;
  }

  return CFG_OK;
}

/**
 * @brief Sets and applies socket config voltage according
 *        to each sockets Chip and SID type
 *
 * @note only run this _after_ a detect_socket_change
 *       returns a detected change and it is validated!!
 *
 */
void apply_socket_config_voltages(void)
{
#if PCB_VERSION_INT >= 15
  if ((usbsid_config.socketOne.chiptype == CHIP_REAL
      && usbsid_config.socketOne.sid1.type == SID_6581)
      || (usbsid_config.socketTwo.chiptype == CHIP_REAL
      && usbsid_config.socketTwo.sid1.type == SID_6581)) {
    /* If 12v is needed we disable all voltages and reconfigure the HV */
    voltage_state_off();
    /* SocketOne */
    if (usbsid_config.socketOne.enabled) {
      if (usbsid_config.socketOne.chiptype == CHIP_REAL) {
        if (usbsid_config.socketOne.sid1.type == SID_6581) {
          set_SID1_highvoltage(true); /* 12v */
        } else {
          set_SID1_highvoltage(false); /* 9v */
        }
      } else {
        set_SID1_highvoltage(false); /* 9v */
      }
    }
    /* SocketTwo */
    if (usbsid_config.socketTwo.enabled) {
      if (usbsid_config.socketTwo.chiptype == CHIP_REAL) {
        if (usbsid_config.socketTwo.sid1.type == SID_6581) {
          set_SID2_highvoltage(true); /* 12v */
        } else {
          set_SID2_highvoltage(false); /* 9v */
        }
      } else {
        set_SID2_highvoltage(false);/* 9v */
      }
    }
    voltage_state_on(); /* Turn on regulators */
  } else { /* Not a real 6581? Then just fire up the 5v and 9v */
    set_base_voltages(100);
  }
#endif
  return;
}

/**
 * @brief verifies the socket configuration loaded from flash
 *        by running a socket change detection if needed
 *        Will turn off regulators if waiting for confirmation
 *        Will otherwise apply requested voltages if no change
 *        is detected or if change detection is disabled
 *
 */
void verify_socket_config(void)
{
#if PCB_VERSION_INT >= 15
  /* Detect changes in socket configuration */
  if (usbsid_config.socket_change_detect) { /* Only continue if enabled, else skip and apply voltages from config! */
    if (!first_boot /* Set by detect default config */
        && !usbsid_config.need_confirmation /* Not already waiting for confirmation */
        && (detect_socket_change() != CFG_OK)) {
      usbsid_config.need_confirmation = detected_sid_change = true;
      /* Disable SID chips */
      voltage_state_off();
      /* Force save the config for confirmation check */
      /* usSOCK("Saving detection result\n"); */
      save_config_ext();
      /* usSOCK("Save done, need_confirmation=%d\n", usbsid_config.need_confirmation); */
    } else if (!usbsid_config.need_confirmation && !detected_sid_change) { /* No changes */
      /* Apply voltage from configurated Chips */
      apply_socket_config_voltages();
    } else if (usbsid_config.need_confirmation && !detected_sid_change) { /* Change detected on previous boot */
      detected_sid_change = true;
      /* Disable SID chips if still enabled */
      voltage_state_off();
    } else if (usbsid_config.need_confirmation || detected_sid_change) { /* Fallback */
      /* Disable SID chips if still enabled */
      voltage_state_off();
    }
  } else { /* Just go with the flow and live dangerously! */
    if (usbsid_config.need_confirmation || detected_sid_change) { /* Fallback check to disable these */
      usbsid_config.need_confirmation = detected_sid_change = false;
      /* usSOCK("Saving detection result\n"); */
      save_config_ext();
      /* usSOCK("Save done, need_confirmation=%d\n", usbsid_config.need_confirmation); */
    }
    /* Apply voltage from configurated Chips */
    apply_socket_config_voltages();
  }
  /* Clear DMA channels and PIO bus afterwards */
  clear_dma_channels();

#endif
  return;
}
