LouDnl/USBSID-Pico/src/midi_defs.h

/*
 * USBSID-Pico is a RPi Pico/PicoW (RP2040) & Pico2/Pico2W (RP2350) based board
 * for interfacing one or two MOS SID chips and/or hardware SID emulators over
 * (WEB)USB with your computer, phone or ASID supporting player
 *
 * midi_defs.h
 * This file is part of USBSID-Pico (https://github.com/LouDnl/USBSID-Pico)
 * File author: LouD
 *
 * Any licensing conditions from either of the above named sources automatically
 * apply to this code
 *
 * Copyright (c) 2024-2026 LouD
 *
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
 */

#ifndef _USBSID_MIDI_CC_H_
#define _USBSID_MIDI_CC_H_
#pragma once

#ifdef __cplusplus
  extern "C" {
#endif


typedef struct midi_ccvalues {
  /* Voice related */
  uint8_t CC_NOTE;  /* Note frequency */
  uint8_t CC_PWM;   /* Pulse Width Modulation (Modulation wheel) */
  uint8_t CC_NOIS;  /* Noise waveform */
  uint8_t CC_PULS;  /* Pulse waveform */
  uint8_t CC_SAWT;  /* Sawtooth waveform */
  uint8_t CC_TRIA;  /* Triangle waveform */
  uint8_t CC_TEST;  /* Test bit */
  uint8_t CC_RMOD;  /* Ring modulator bit */
  uint8_t CC_SYNC;  /* Sync bit */
  uint8_t CC_GATE;  /* Gate bit */
  uint8_t CC_ATT;   /* Attack */
  uint8_t CC_DEC;   /* Decay */
  uint8_t CC_SUS;   /* Sustain */
  uint8_t CC_REL;   /* Release */
  /* Chip related */
  uint8_t CC_FFC;   /* Filter Frequency Cutoff */
  uint8_t CC_RES;   /* Filter resonance */
  uint8_t CC_FLT1;  /* Filter voice 1 */
  uint8_t CC_FLT2;  /* Filter voice 2 */
  uint8_t CC_FLT3;  /* Filter voice 3 */
  uint8_t CC_FLTE;  /* Filter external */
  uint8_t CC_3OFF;  /* Voice 3 disconnect */
  uint8_t CC_HPF;   /* High pass */
  uint8_t CC_BPF;   /* Band pass */
  uint8_t CC_LPF;   /* Low pass */
  uint8_t CC_VOL;   /* Channel Volume */
  /* SID / Voice selection */
  uint8_t CC_SID1;  /* Select SID 1 */
  uint8_t CC_SID2;  /* Select SID 2 */
  uint8_t CC_SID3;  /* Select SID 3 */
  uint8_t CC_SID4;  /* Select SID 4 */
  uint8_t CC_VCE1;  /* Select Voice 1 */
  uint8_t CC_VCE2;  /* Select Voice 2 */
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
